Severson-Group/AMDS/Mainboard/REV20200407C/README.md

This folder contains schematics pdf, PCB pdf, bill of material (BOM), 3-D PCB, gerber files and all the required files to fabricate the boards.

## How to order 10 PCB boards

1. Place a new quote in https://www.pcbway.com/ 

2. Use the following table to set the pcb properties.

| Question | Answer |
|---|---|
|Size| 203.4 x 203.4 mm|
|Layer| 4 Layers|
|Quantity| 10|
|Board type| Single pieces|
|Different Design in Panel| 1|
|Material: FR-4| TG150|
|Thickness| 1.6 mm|
|Min Track/Spacing| 6/6mil|
|Min Hole Size| 0.3mm|
|Solder Mask| Black|
|Silkscreen| White|
|Gold fingers| No|
|Surface Finish| HASL with lead|
|"HASL" to "ENIG"| No|
|Via Process| Tenting vias|
|Finished Copper| 1 oz Cu (Inner Copper: 1 oz)|
|Additional options| UL Marking: None|

3. Upload the gerbers from `SensorMotherBoard_REVC_Gerber\` folder.

4. Place the order, it should arrive in 7-9 days.

## How to order components for the board

1. The components sheet can be found in `SensorMotherBoard_REVC_BOM\` folder.

2. Upload the BOM sheet in https://www.digikey.com/ordering/shoppingcart.

3. Place the order.
