Severson-Group/AMDS/CurrentCard/REV20190618A/README.md

# SensorCard
Voltage and Current Sense Board
