Severson-Group/AMDS/Accessories/DaisyChainAdapter/REV20260129A/README.md

# Daisy Chain Adapter REV20260129A

This folder contains the compiled design outputs for the Daisy Chain Adapter. This includes the schematics, images of the PCB layout, the bill of materials (BOM), and the files needed to order fully populated boards from an online vendor.

## Board Parameters

| Question | Answer |
|---|--- |
| Board Size | 2.17" x 2.80" |
| Number of Layers | 4 Layers |
| Double Sided | Yes |
| Surface Finish | Tin lead |
| Silkscreen | White |
| Material | FR-4, TG150 |
| Board Thickness | 1.6 mm |
| Min Trace Spacing | 0.127 mm (5 mil) |
| Min Hole Size | 0.36 mm (14 mil) |
| Number of Holes | 78 |
| Solder Mask | Green |
| HASL or ENIG | No |
| Finished Copper | 1 oz |

## Assembly Details

| Question | Answer |
|---|---|
| Unique Part Count[^1] | 14 |
| Number of Total Parts[^1] | 29 |
| Total SMT Part Count | 26 |
| Total Through-hole Part Count | 3 |
| Total Mechanical Screws | 4 |
| Total Mechanical Standoffs | 4 |
| BGA / QFN | No |

## Bill of Materials

The [Bill of Materials (BOM)](daisy-chain-bom.csv) contains components for 1 board. If users of this repo discover that any components are unavailable, please maintain an `alternate-components.md` file in this folder that lists approved alternates.

[^1]: This number does not include screws or standoffs. With screws and standoffs included, the unique part count is 16 and total parts is 37. Users are advised to not have their assembly vendor place screws and standoffs.
