Severson-Group/AMDS/CurrentCard/REV20190618A/CurrentSensorBoard.pdf

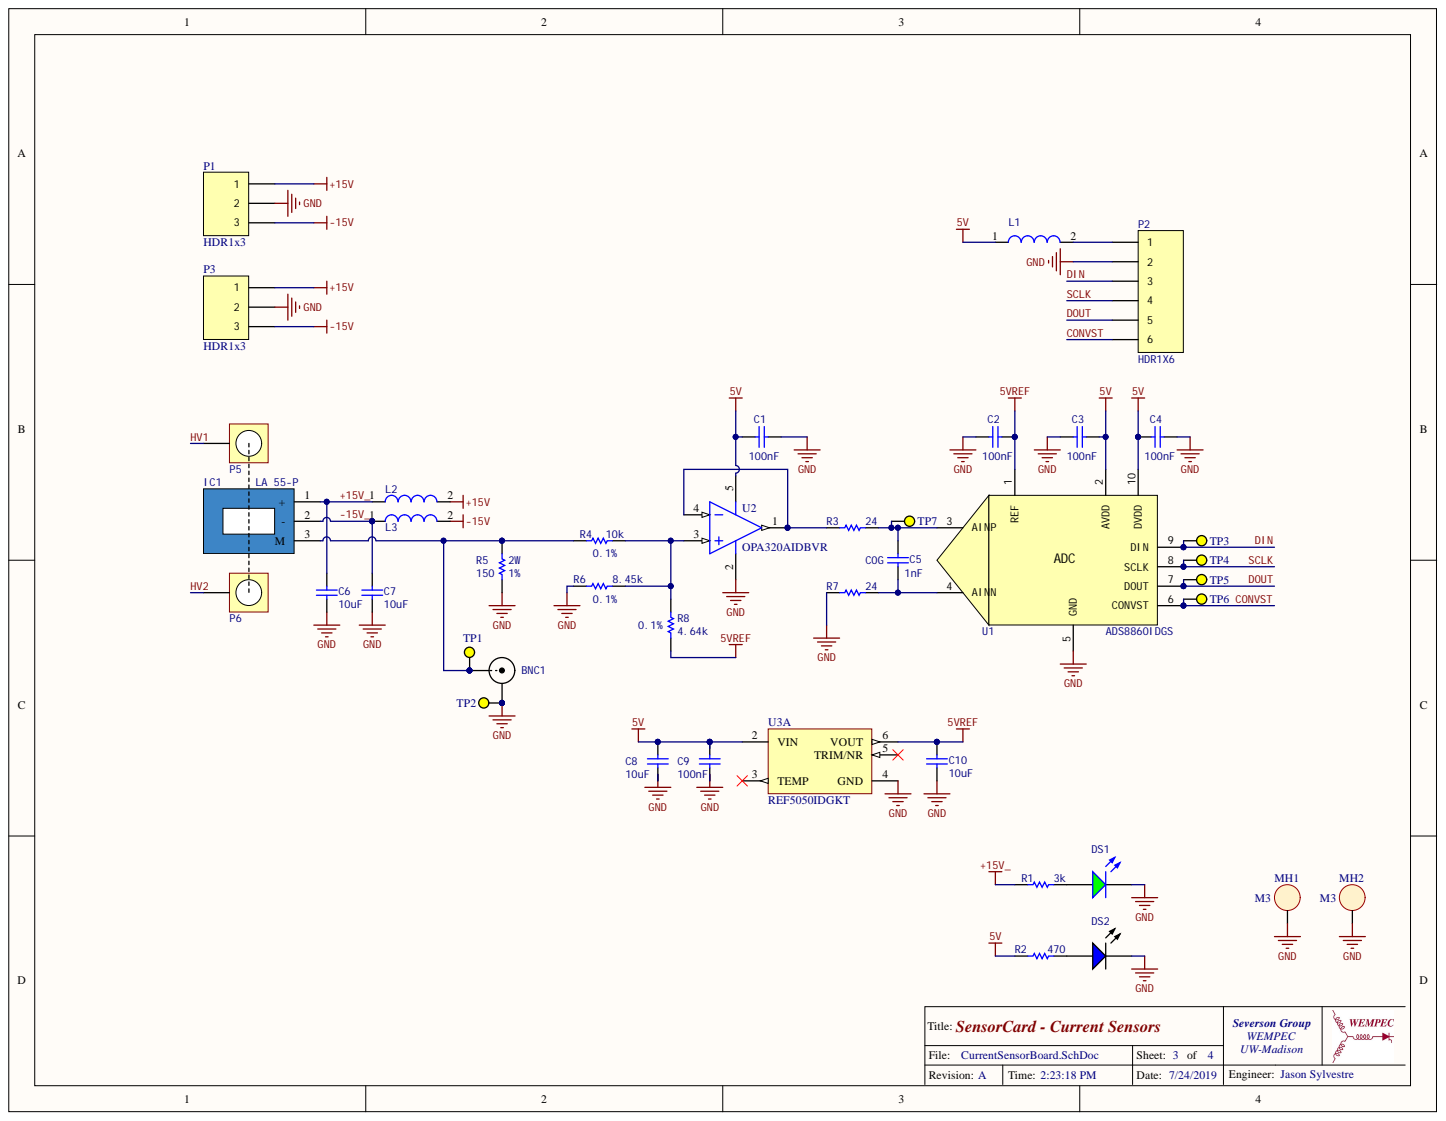
[picture p28: page 1]

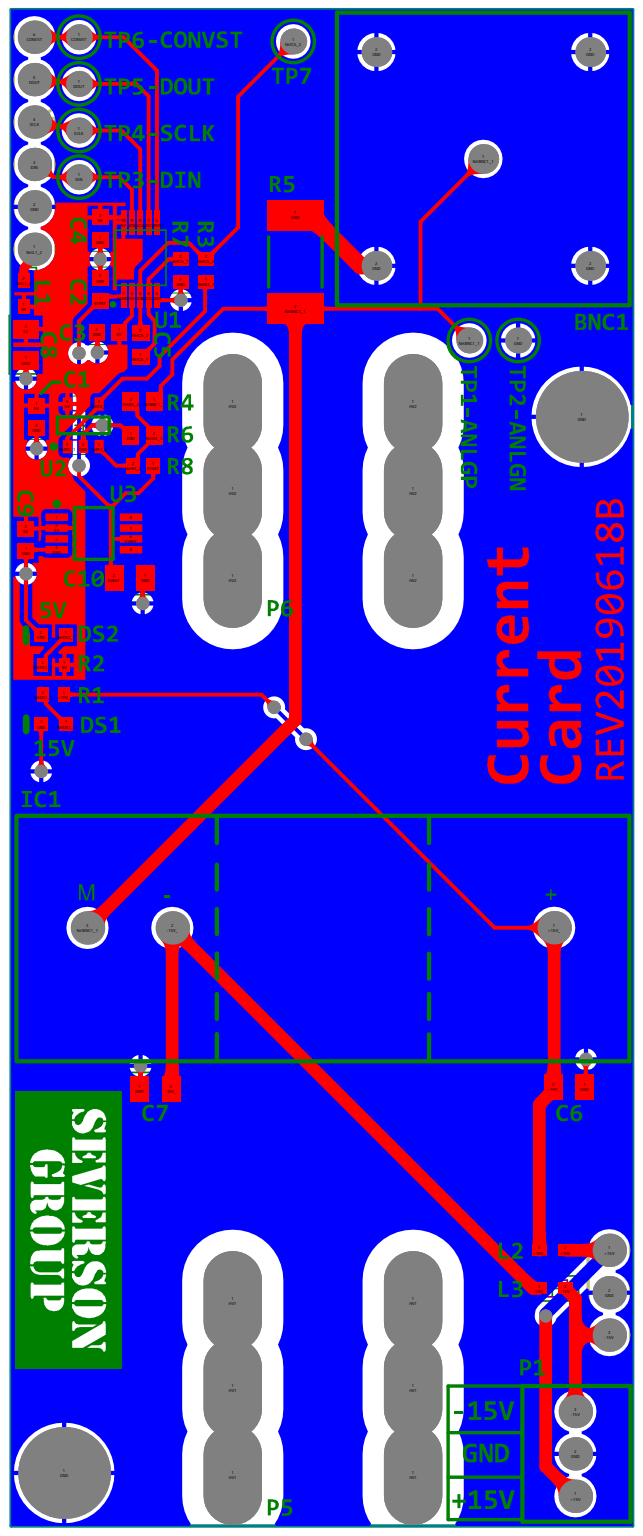
[picture p29: page 2]

2 NetC5_1 | 2 NetC5_2

GND

GND 1 GND | 5VREF 5
