Severson-Group/AMDS/CurrentCard/REV20190805B/CurrentSensorBoard.pdf

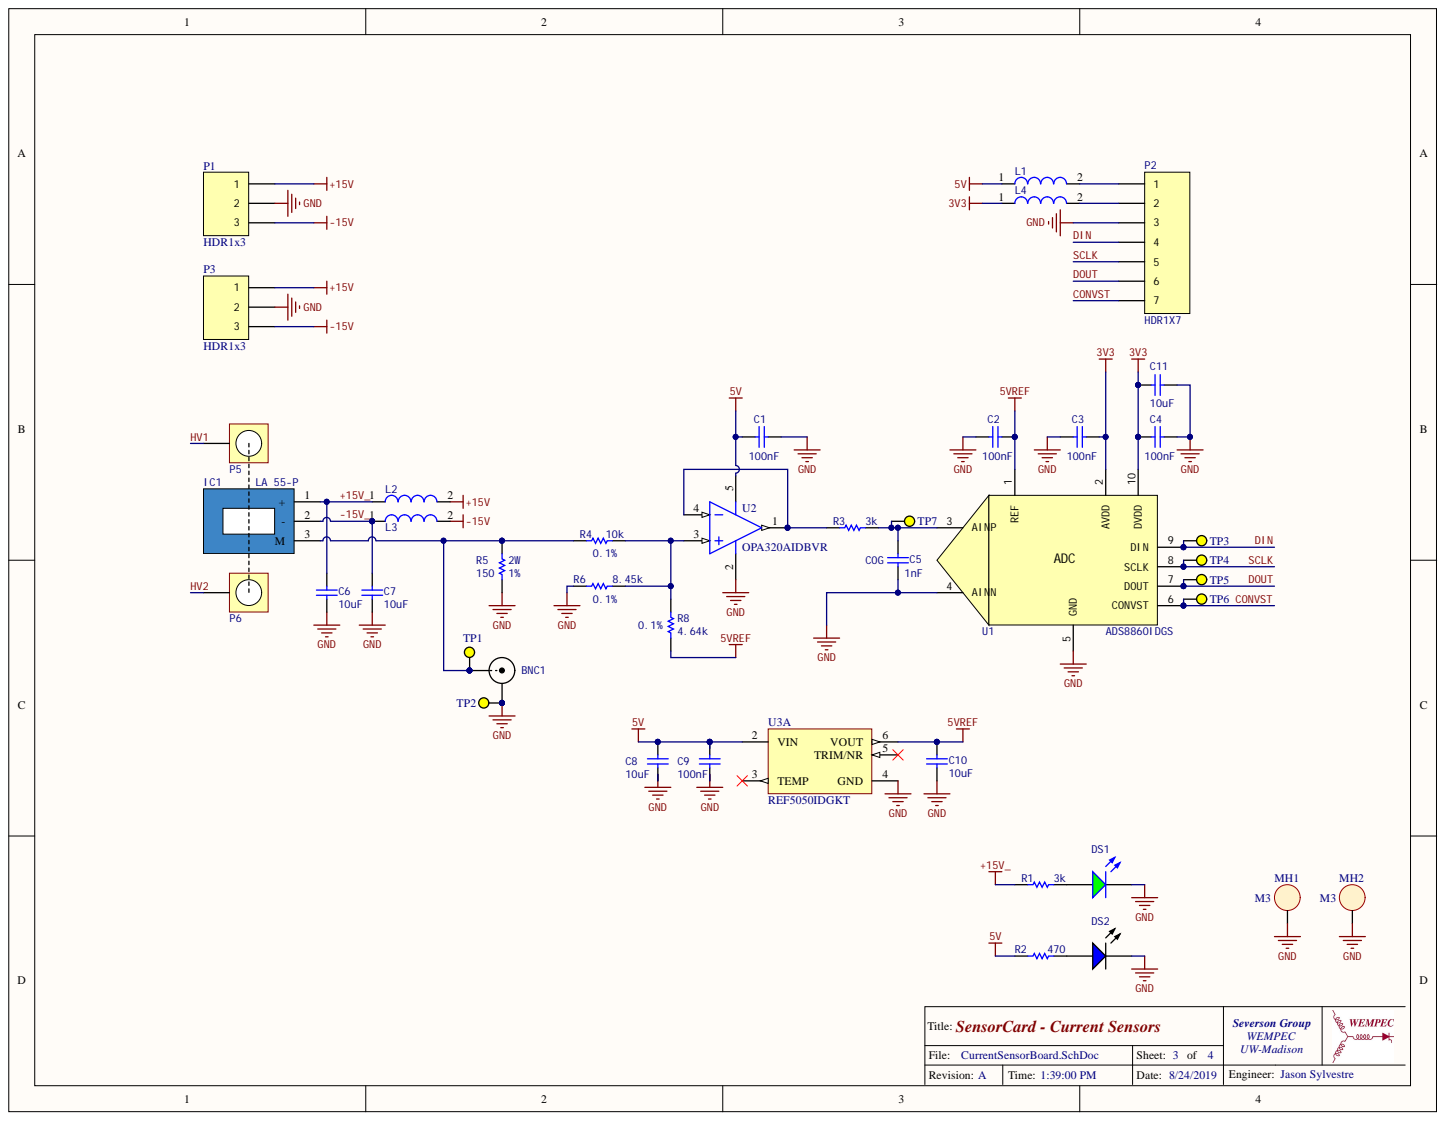
[picture p30: page 1]

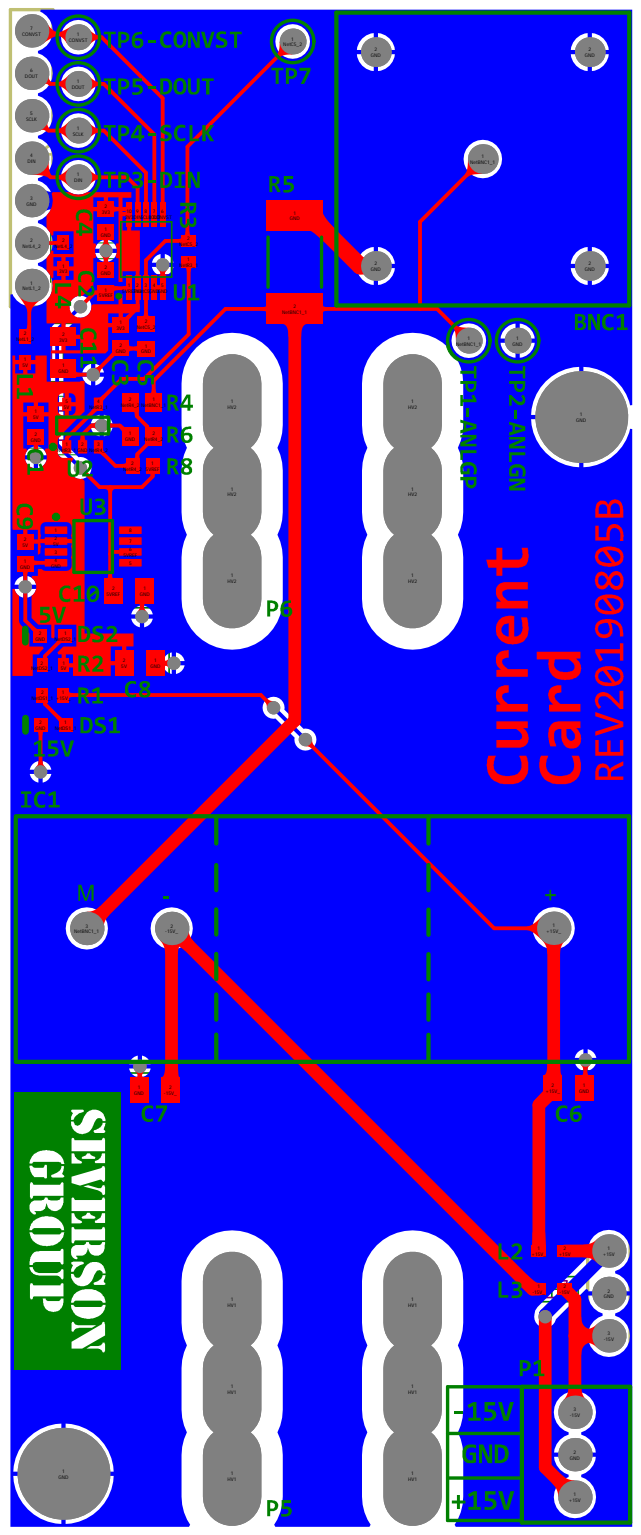
[picture p31: page 2]

1 GND GND | 5VREF 5
