Severson-Group/AMDS/HighVoltageCard/REV20190618A/VoltageSensorBoard.pdf

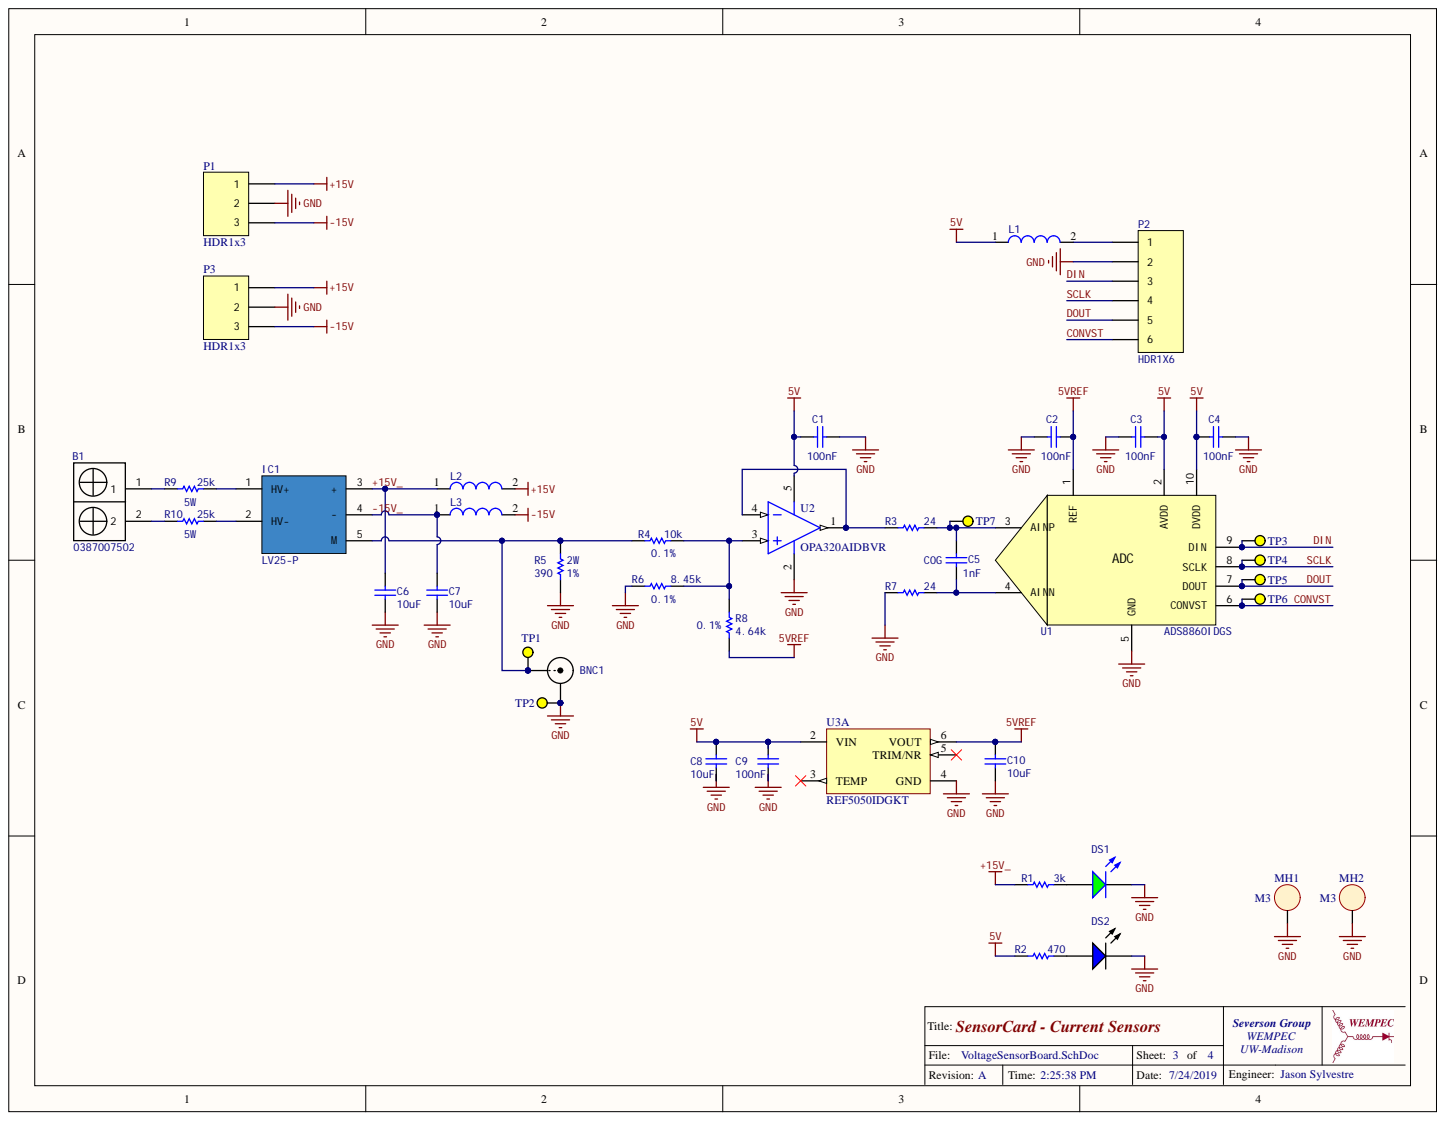
[picture p32: page 1]

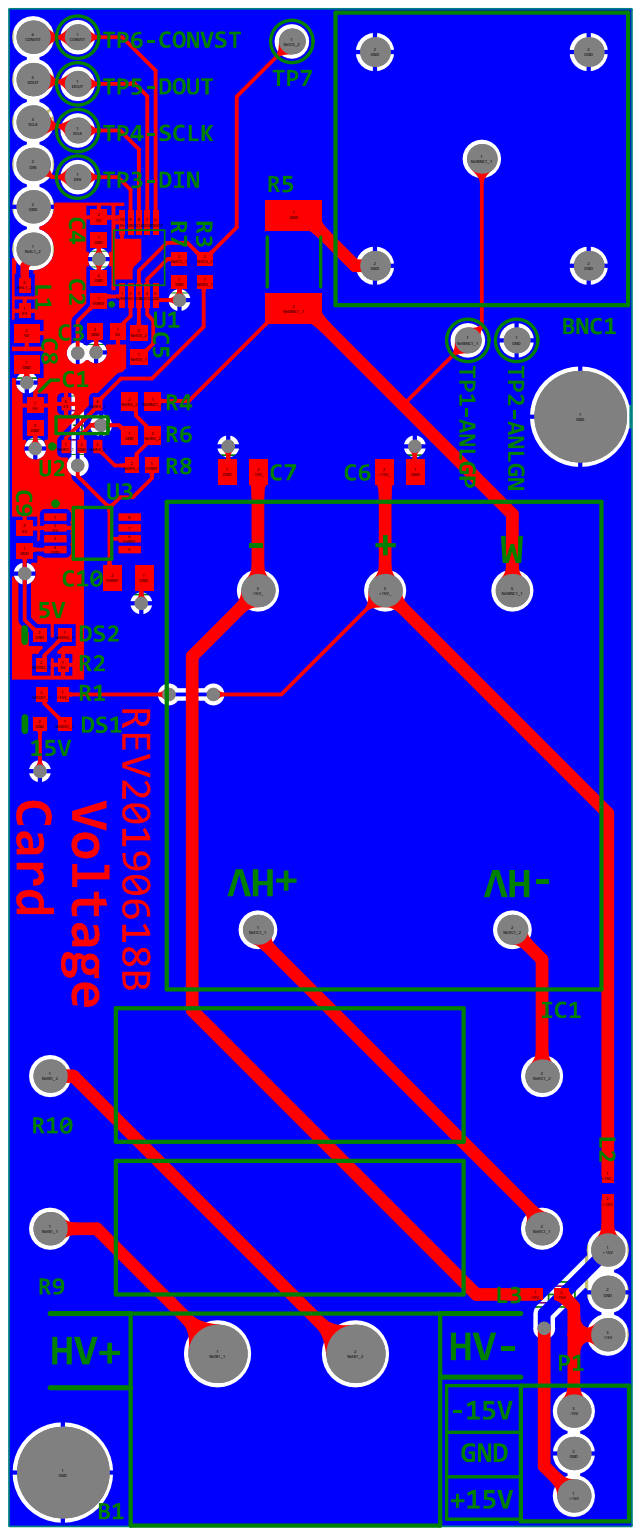
[picture p33: page 2]

2 NetC5_1 | 2 NetC5_2

1 5V | 5 5V | NetR3_1 | 2 | 1 NetBNC1_1

NetDS1_1 2 +15V_ 1 | NetIC1_1 NetIC1_1 1 1
