Severson-Group/AMDS/HighVoltageCard/REV20190805B/VoltageSensorBoard.pdf

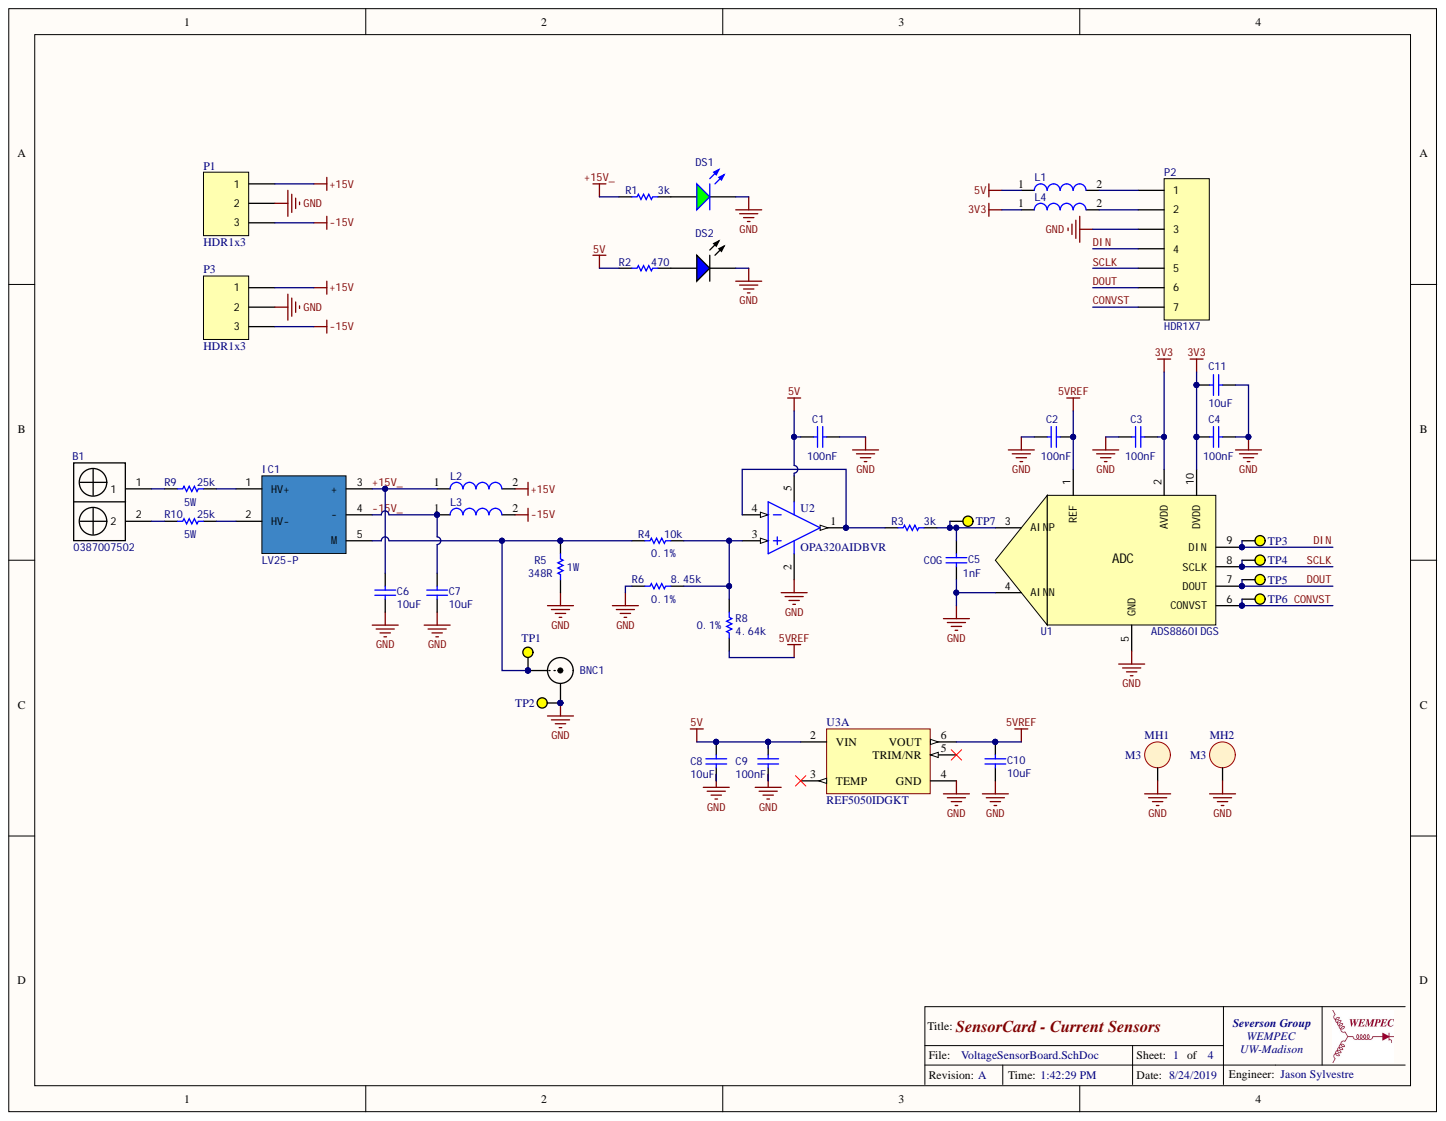
[picture p34: page 1]

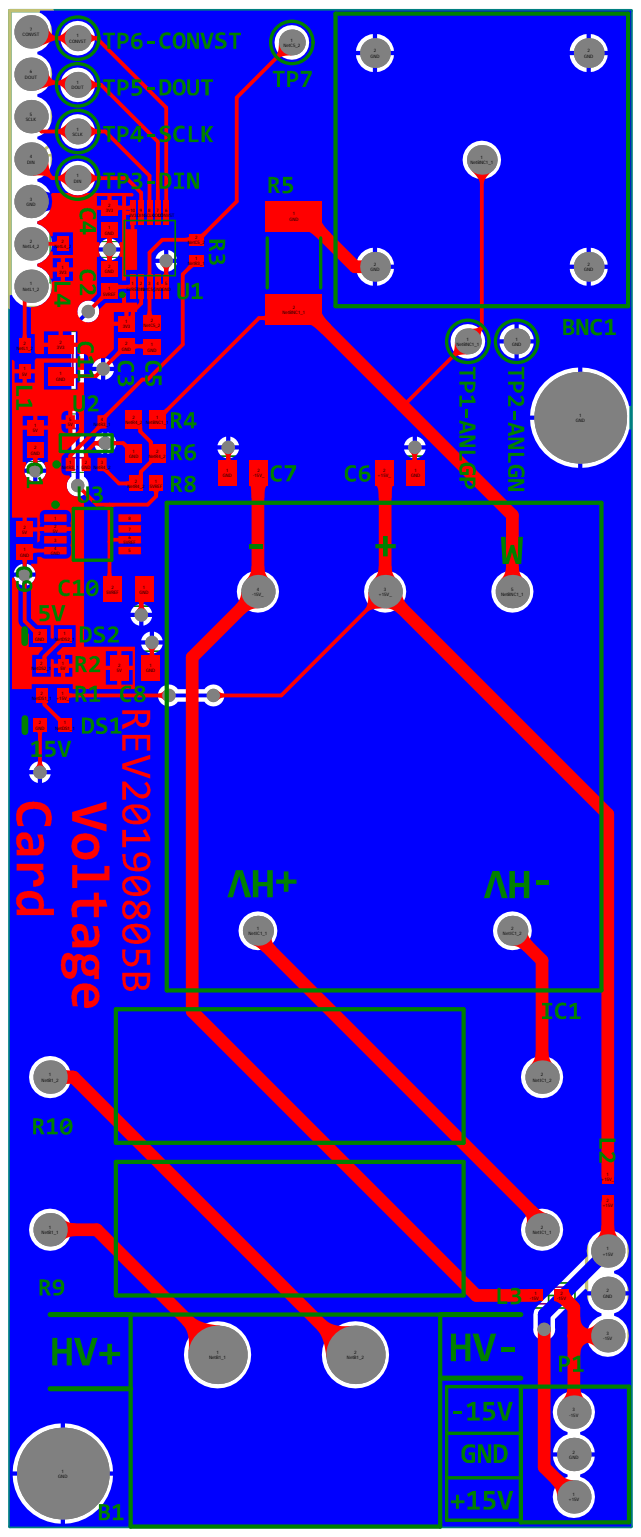
[picture p35: page 2]

5V | GND

NetDS1_1 2 +15V_ 1 | NetIC1_1 NetIC1_1 1 1
