Severson-Group/AMDS/Mainboard/REV20190805B/SensorMotherBoard.pdf

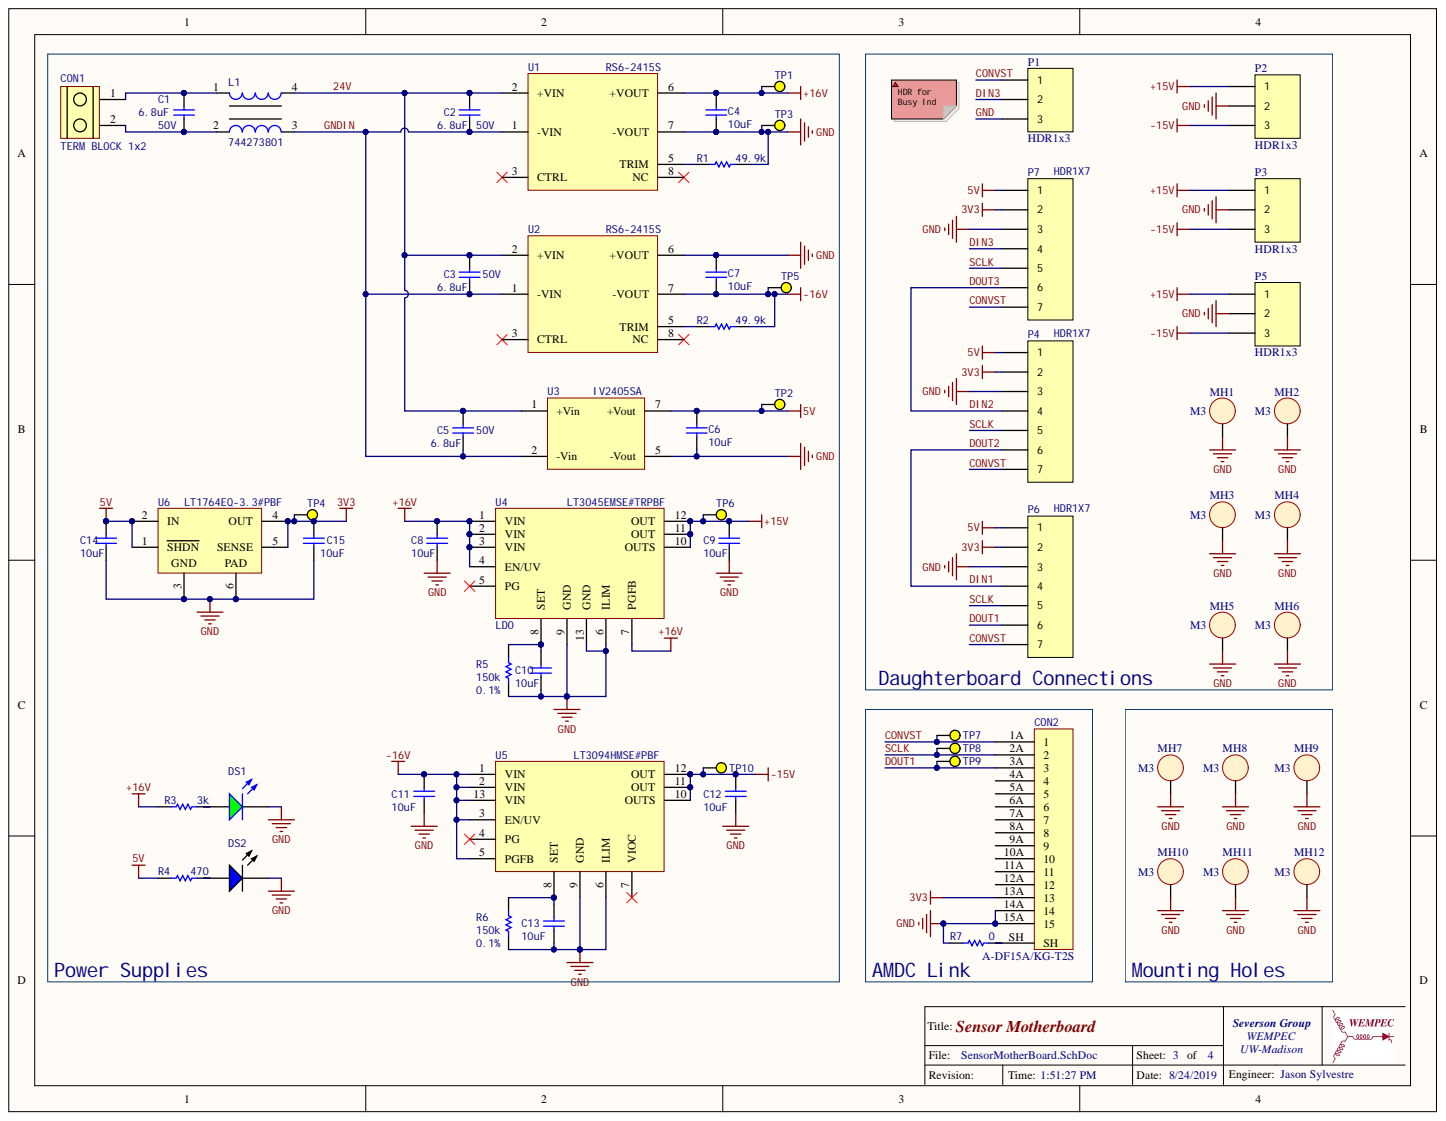
[picture p36: page 1]

C3 50V | -VIN 1 | C7 TP5

CONVST

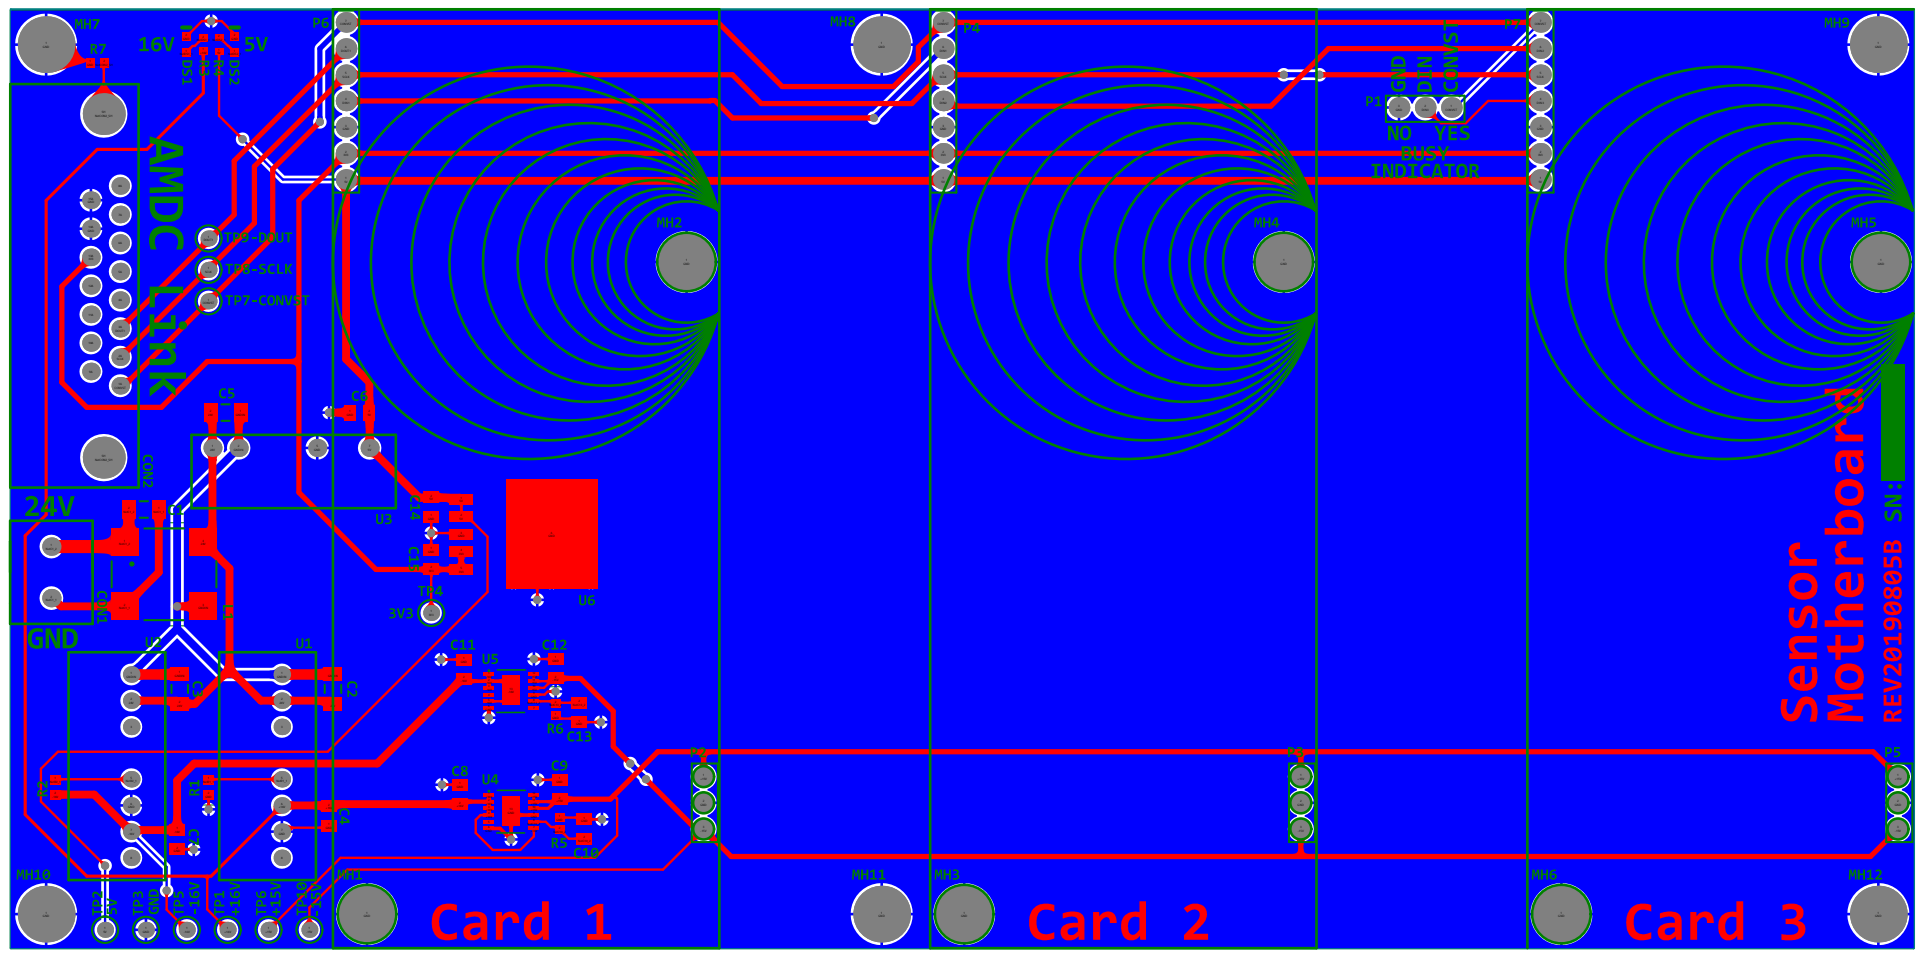
[picture p37: page 2]
