Severson-Group/AMDS/CurrentCard/REV20200830C/pcb-layers.pdf

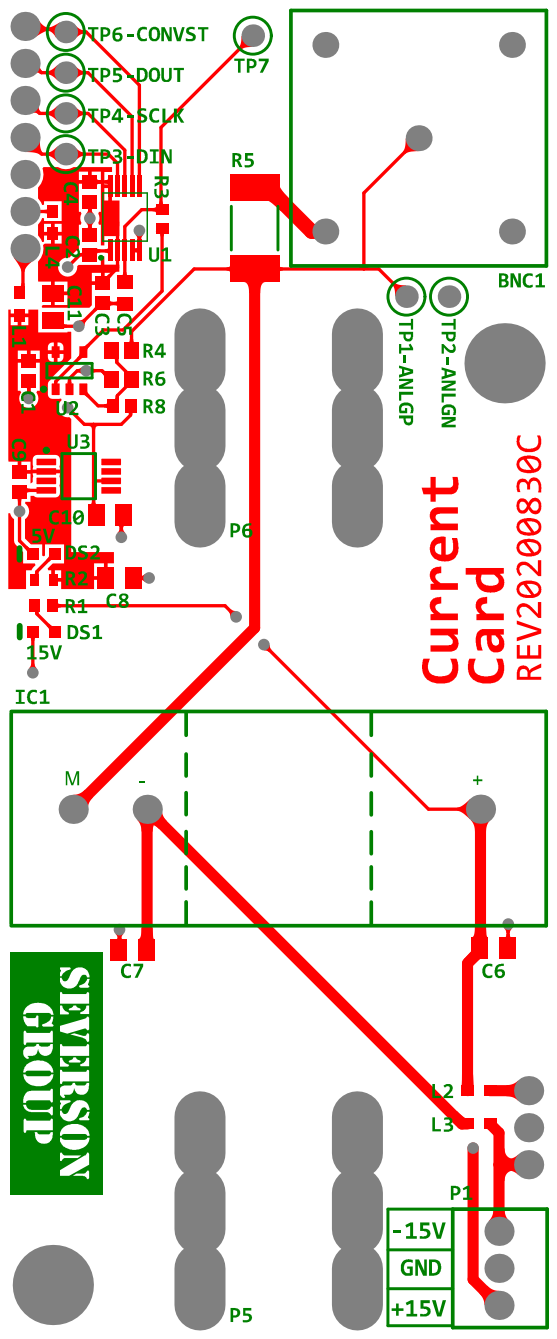
[picture p44: page 1]

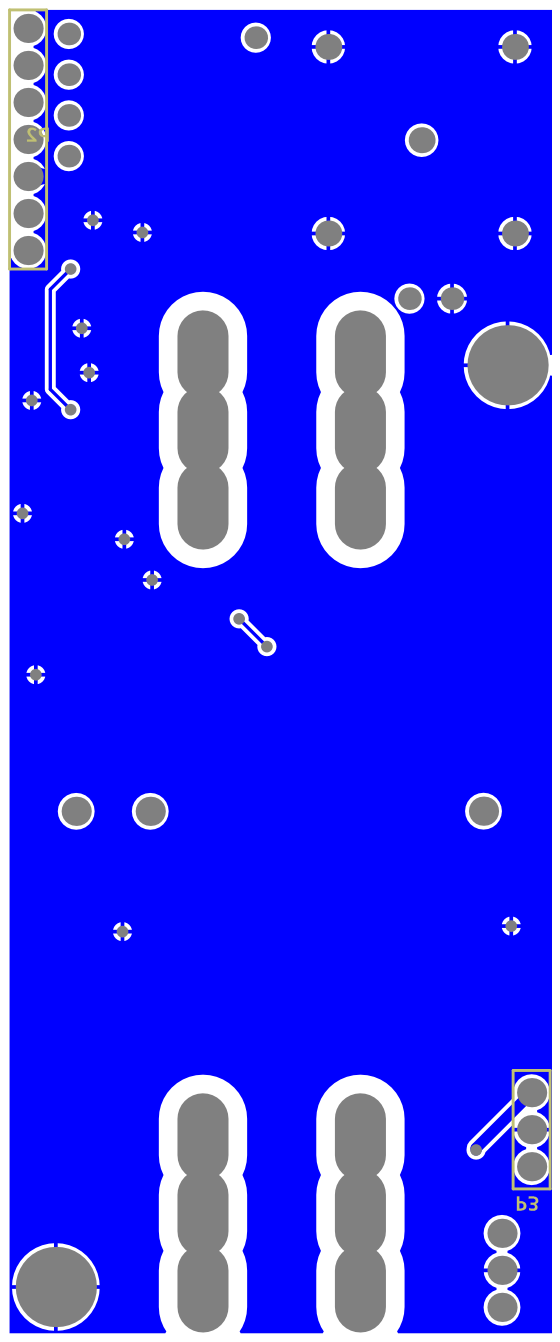
[picture p45: page 2]
