Severson-Group/AMDS/Mainboard/REV20200920D/pcb-layers.pdf

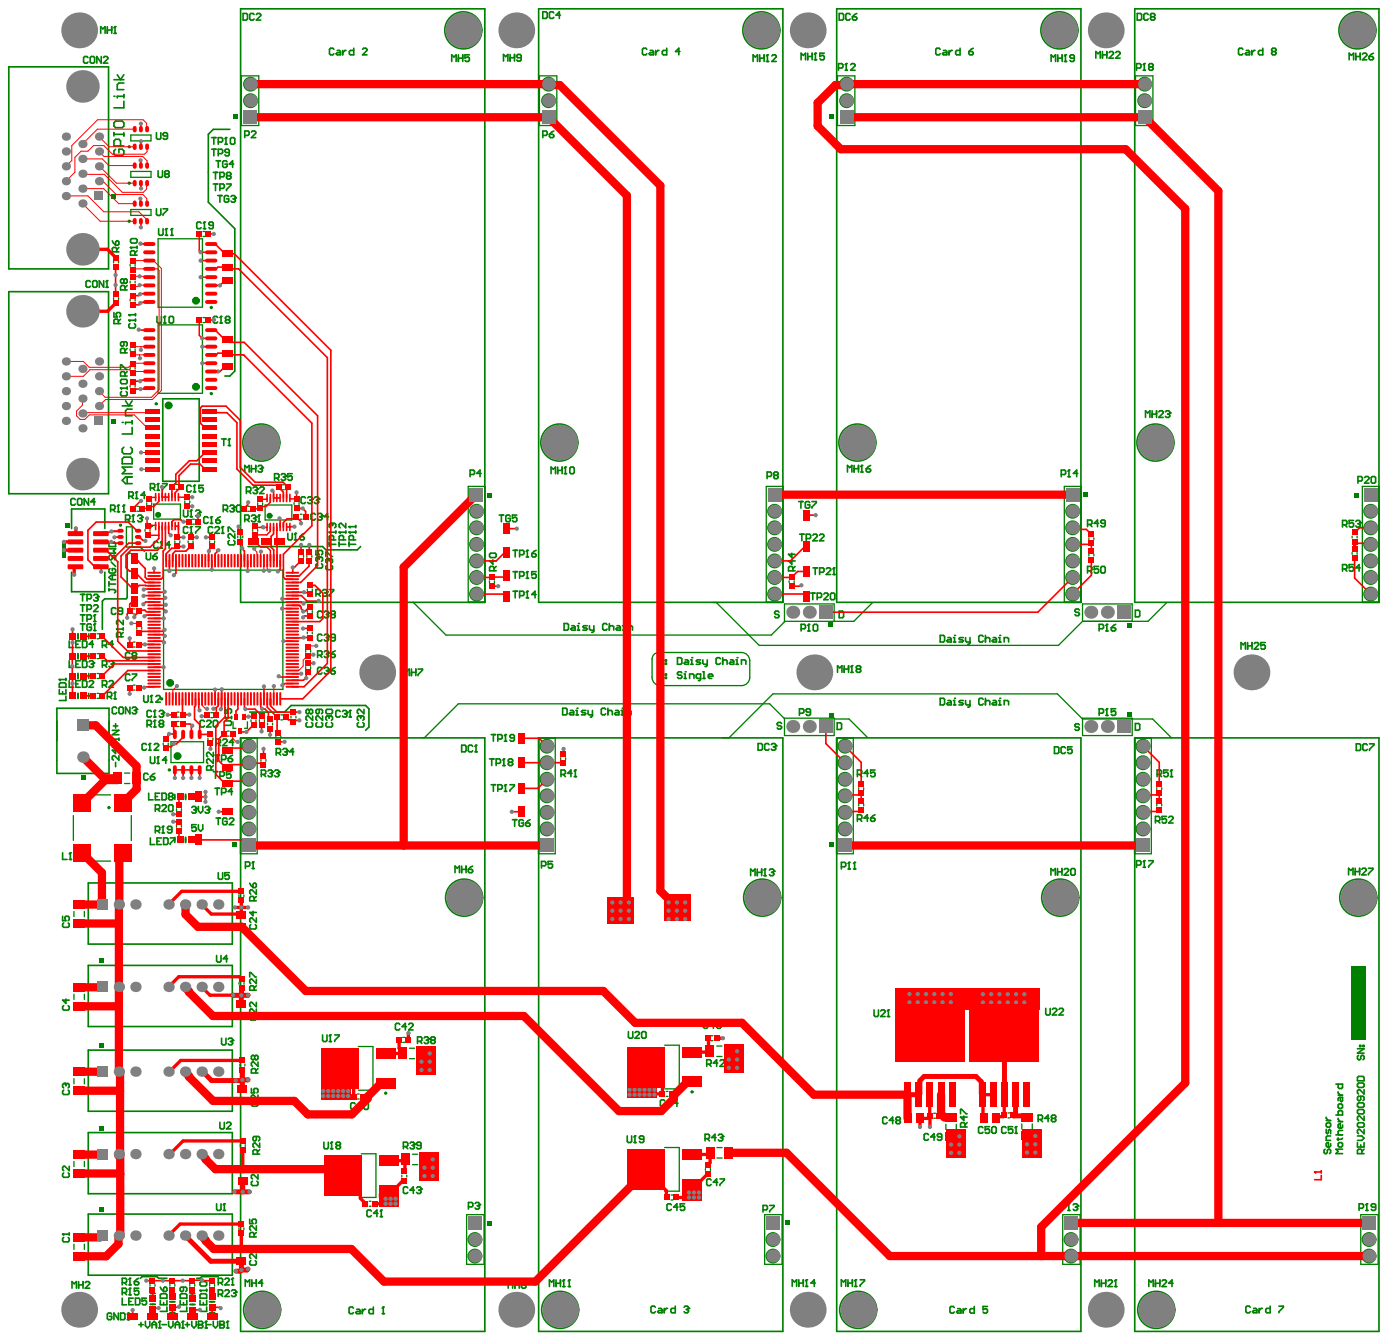
[picture p46: page 1]

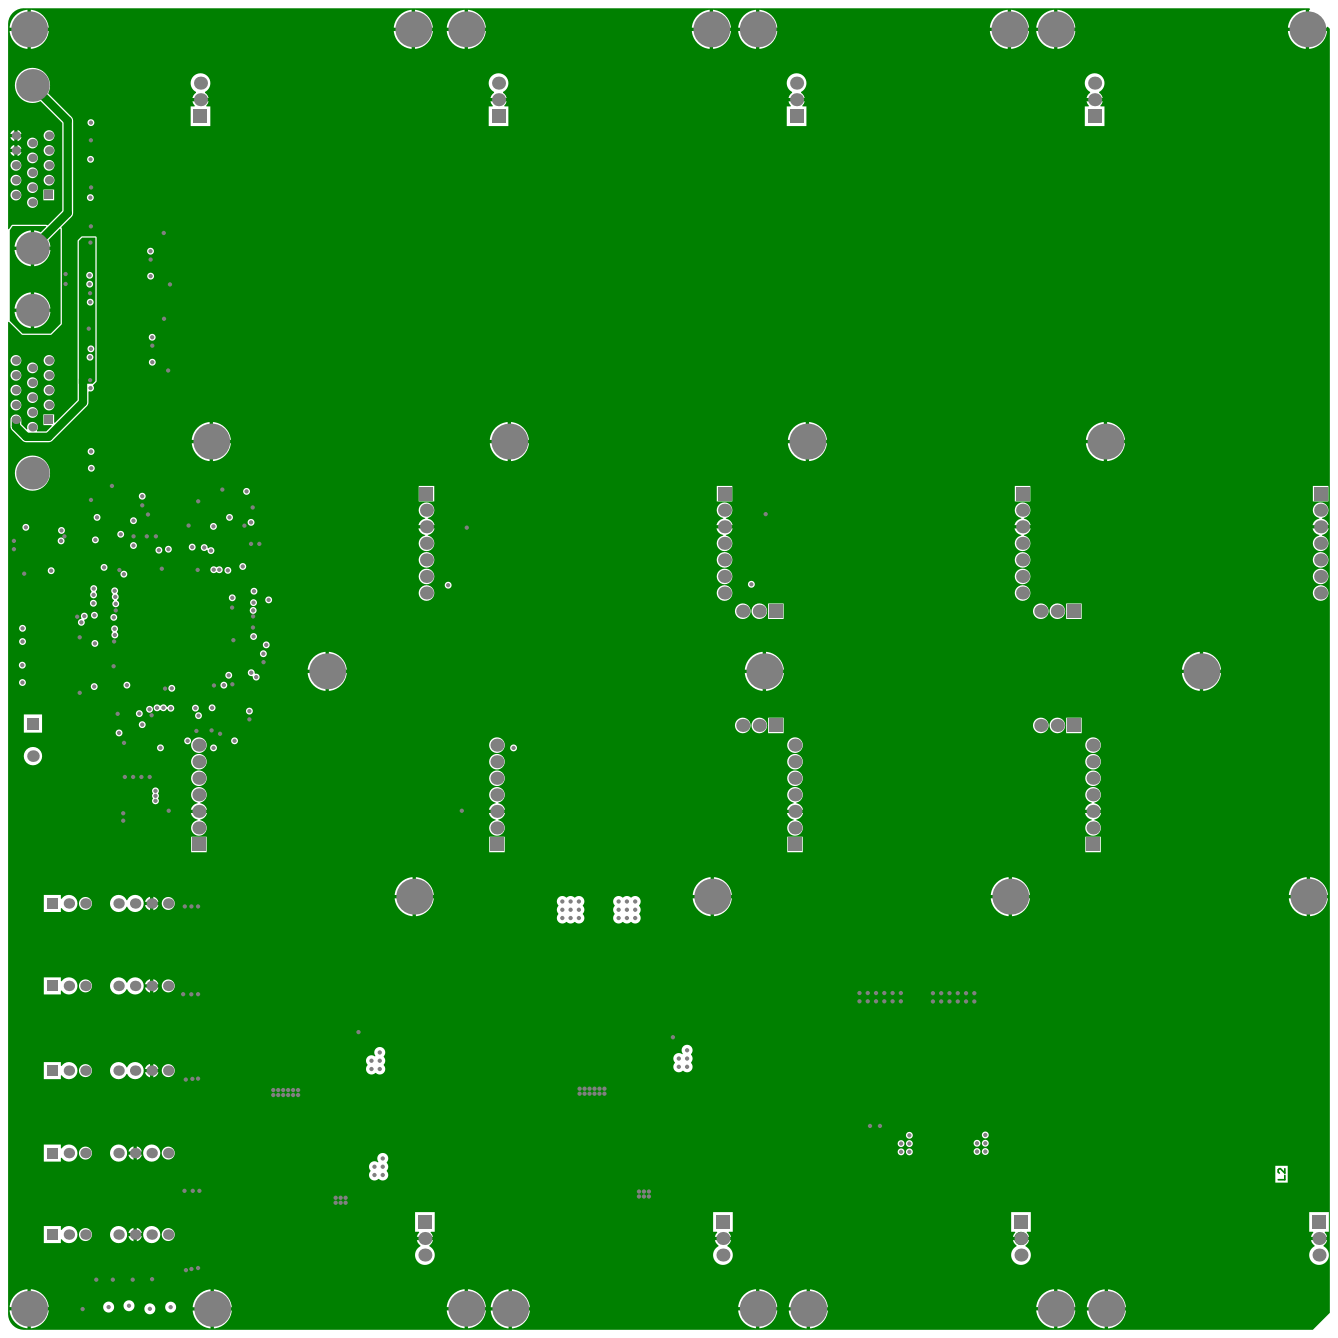
[picture p47: page 2]

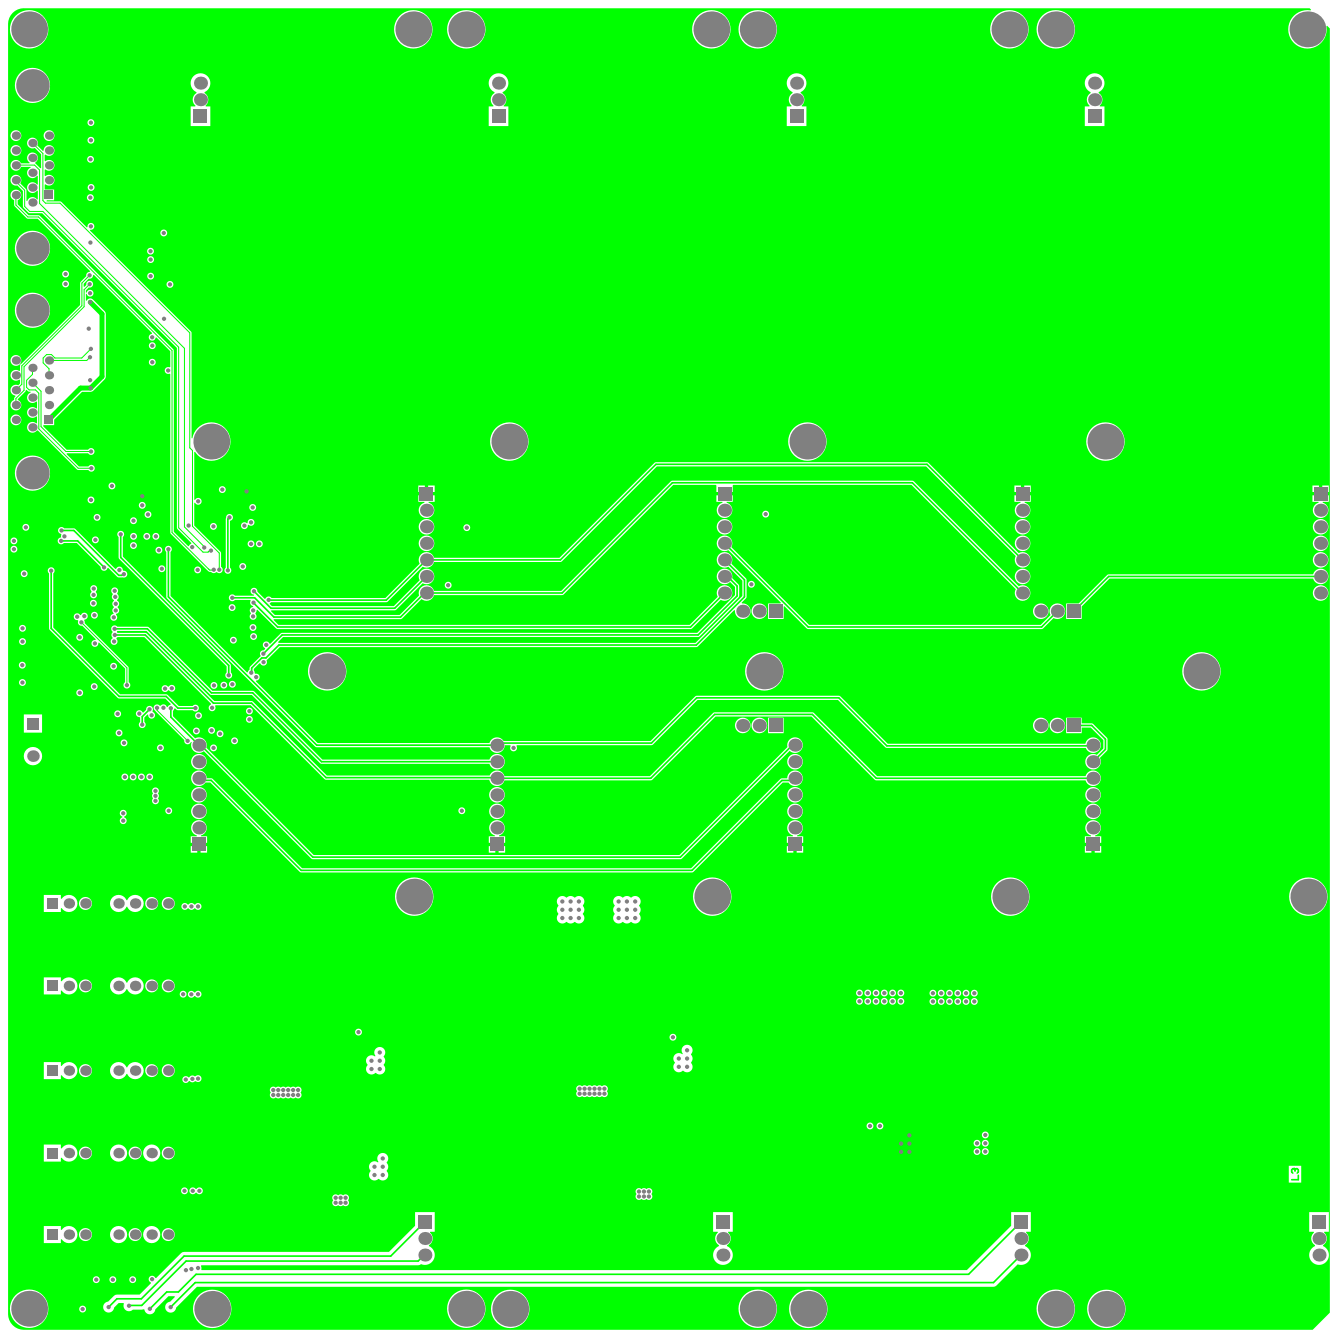
[picture p48: page 3]

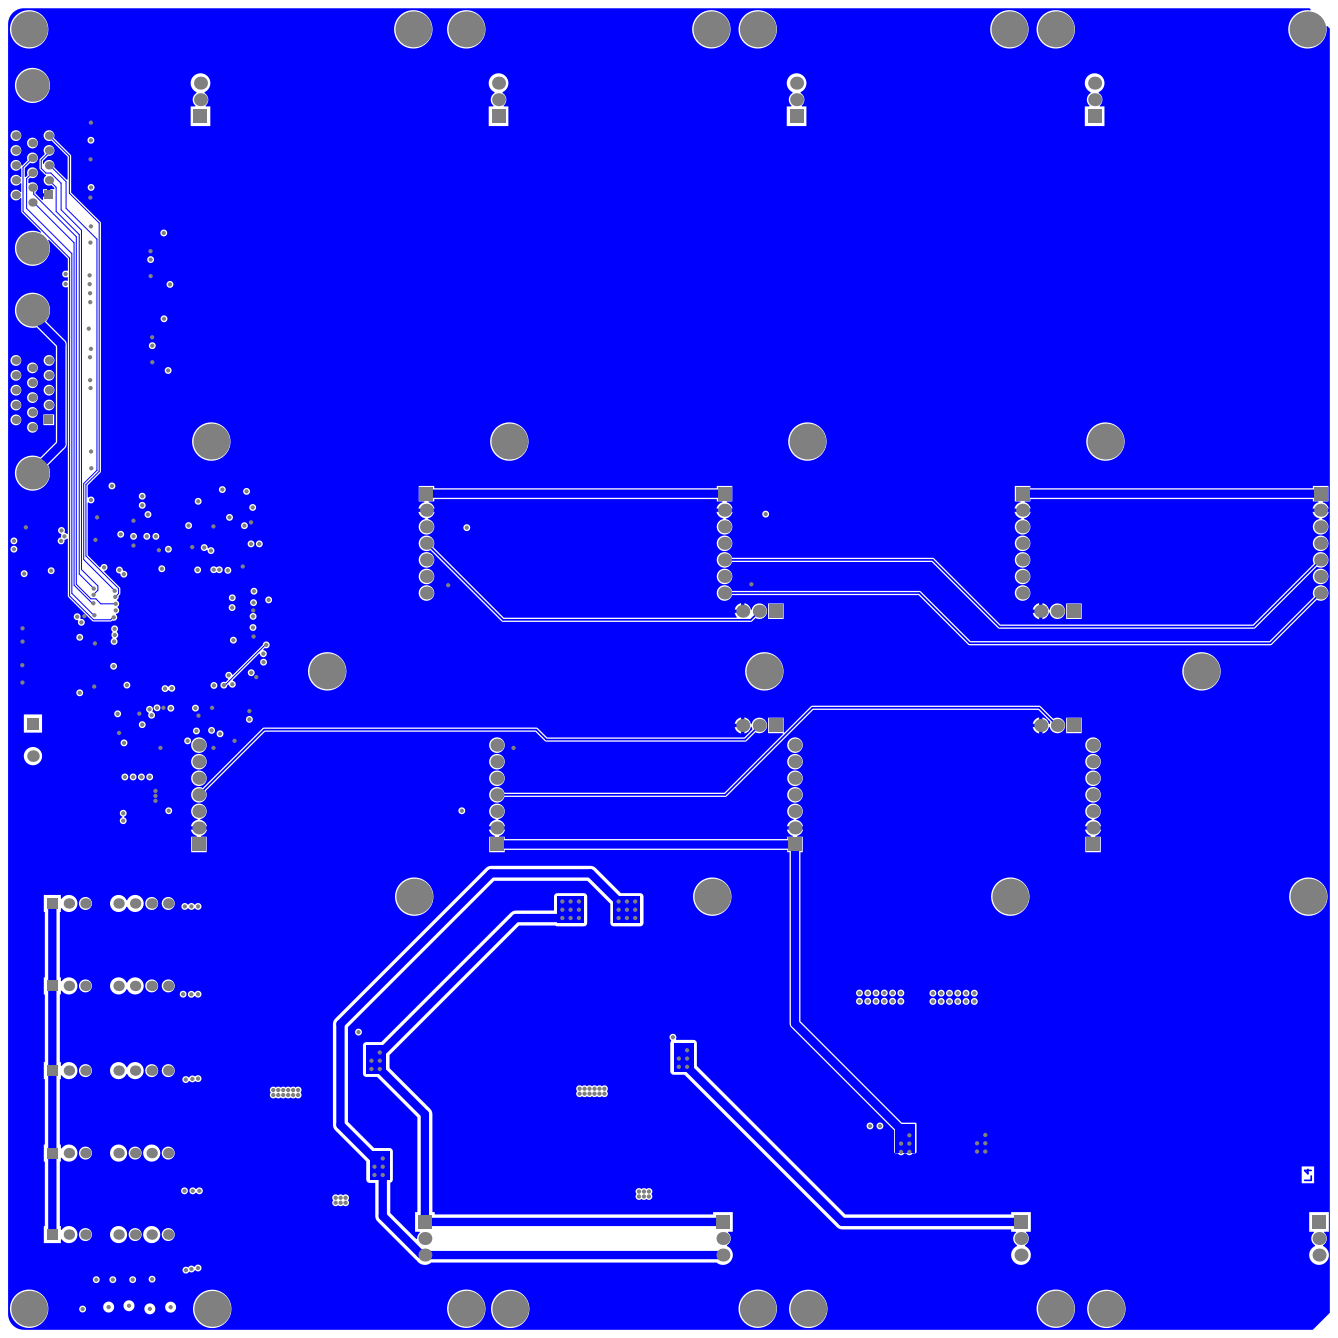
[picture p49: page 4]
