Severson-Group/AMDS/Mainboard/REV20190714A/SensorMotherBoard.pdf

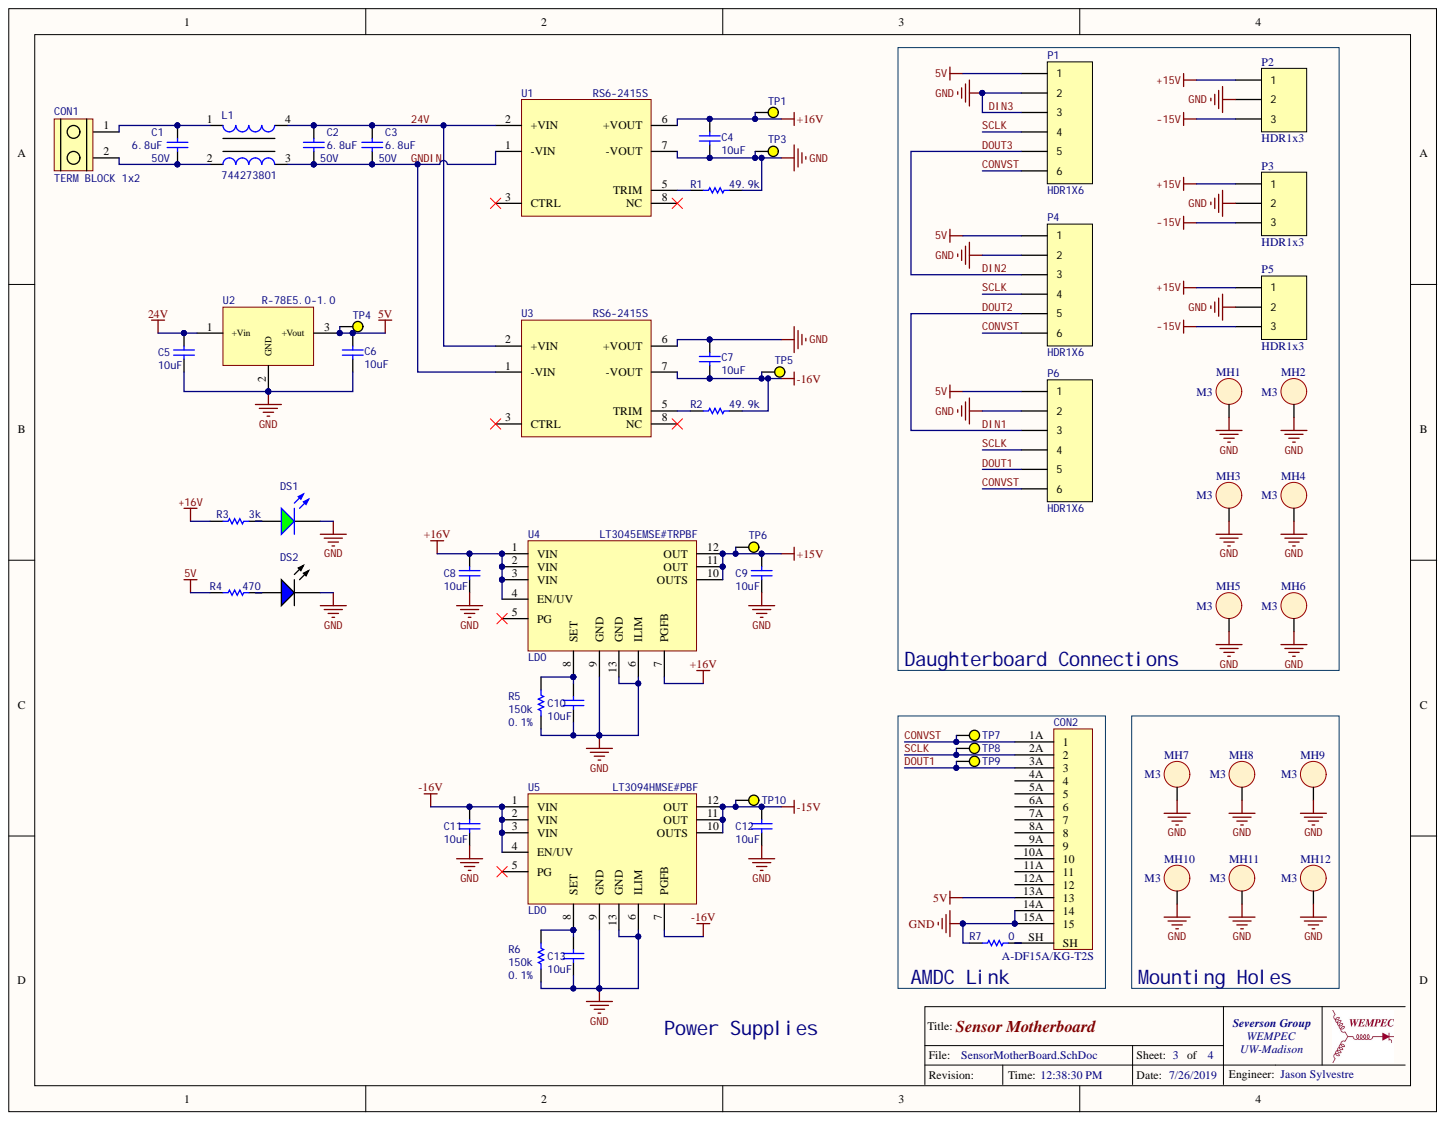
[picture p50: page 1]

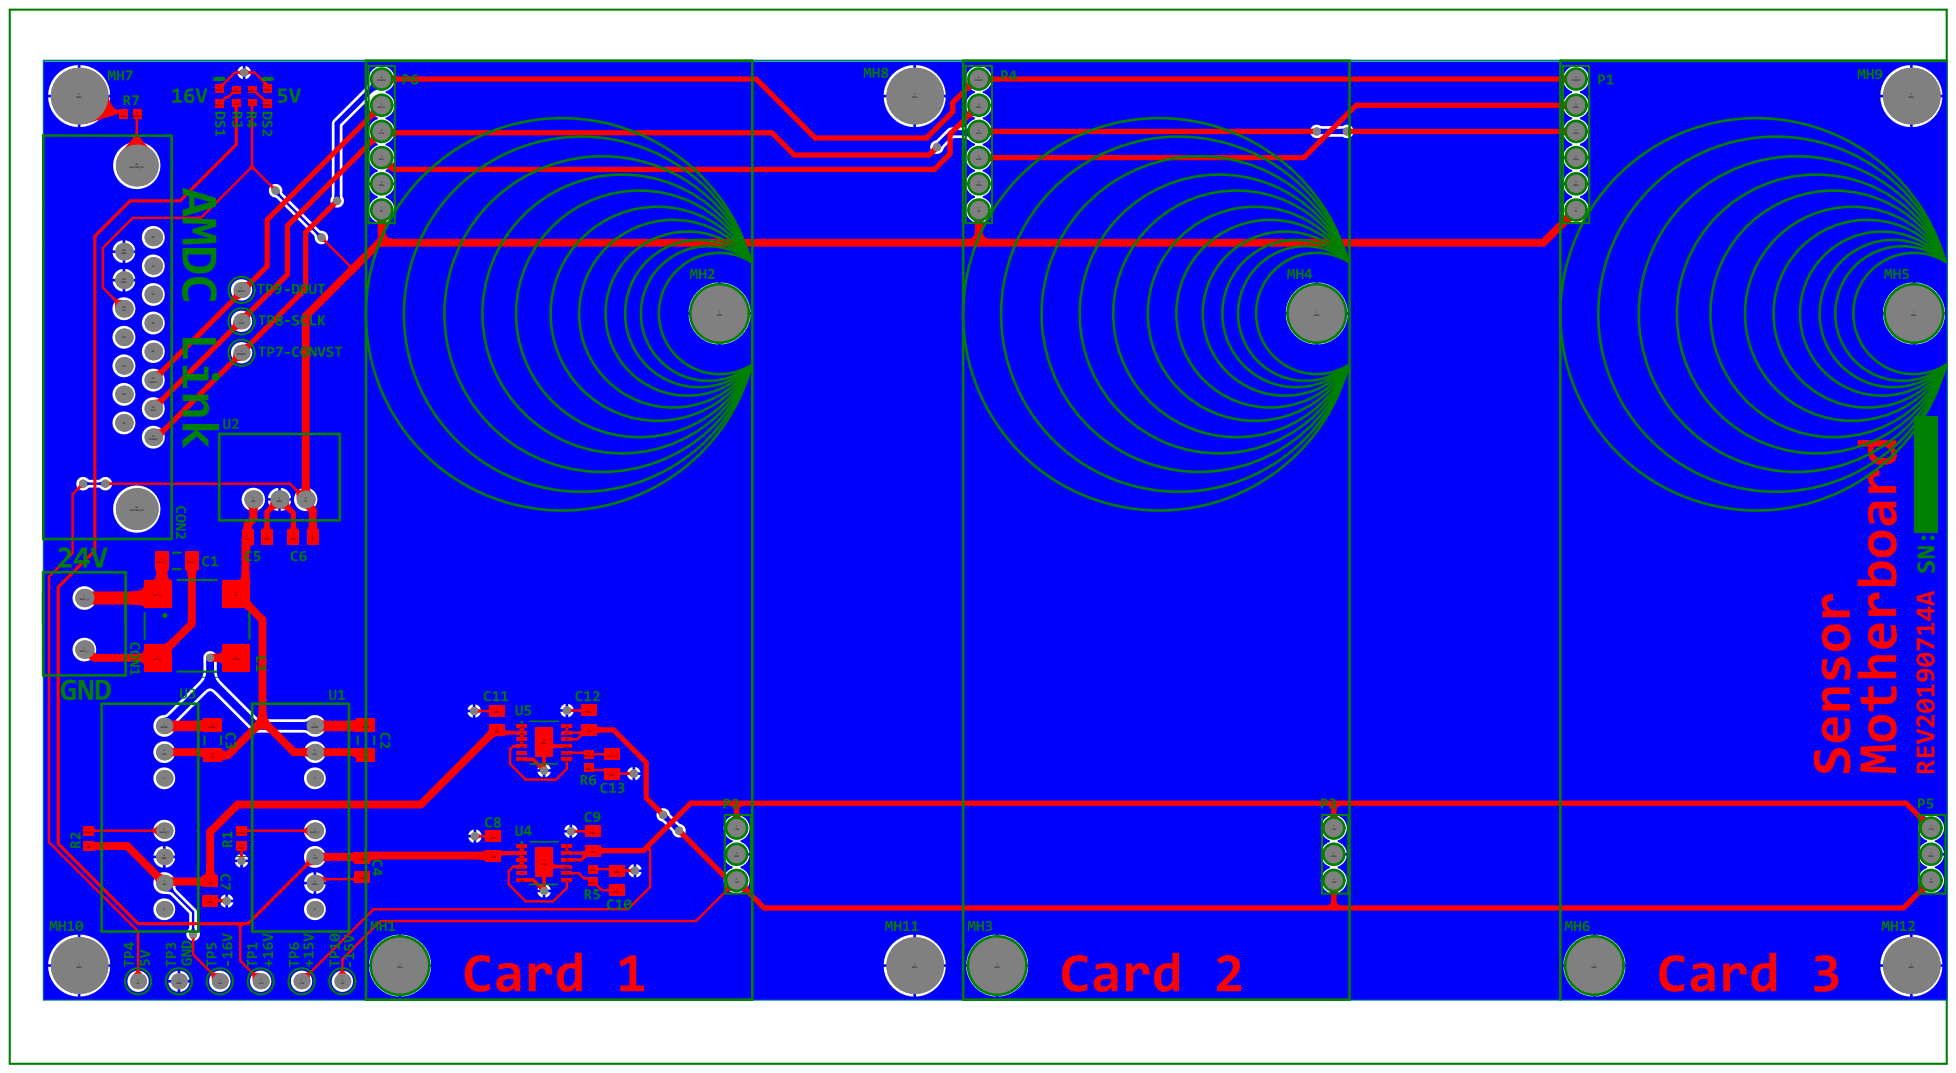
[picture p51: page 2]
