Severson-Group/AMDS/Accessories/DaisyChainAdapter/REV20260129A/pcb-layers.pdf

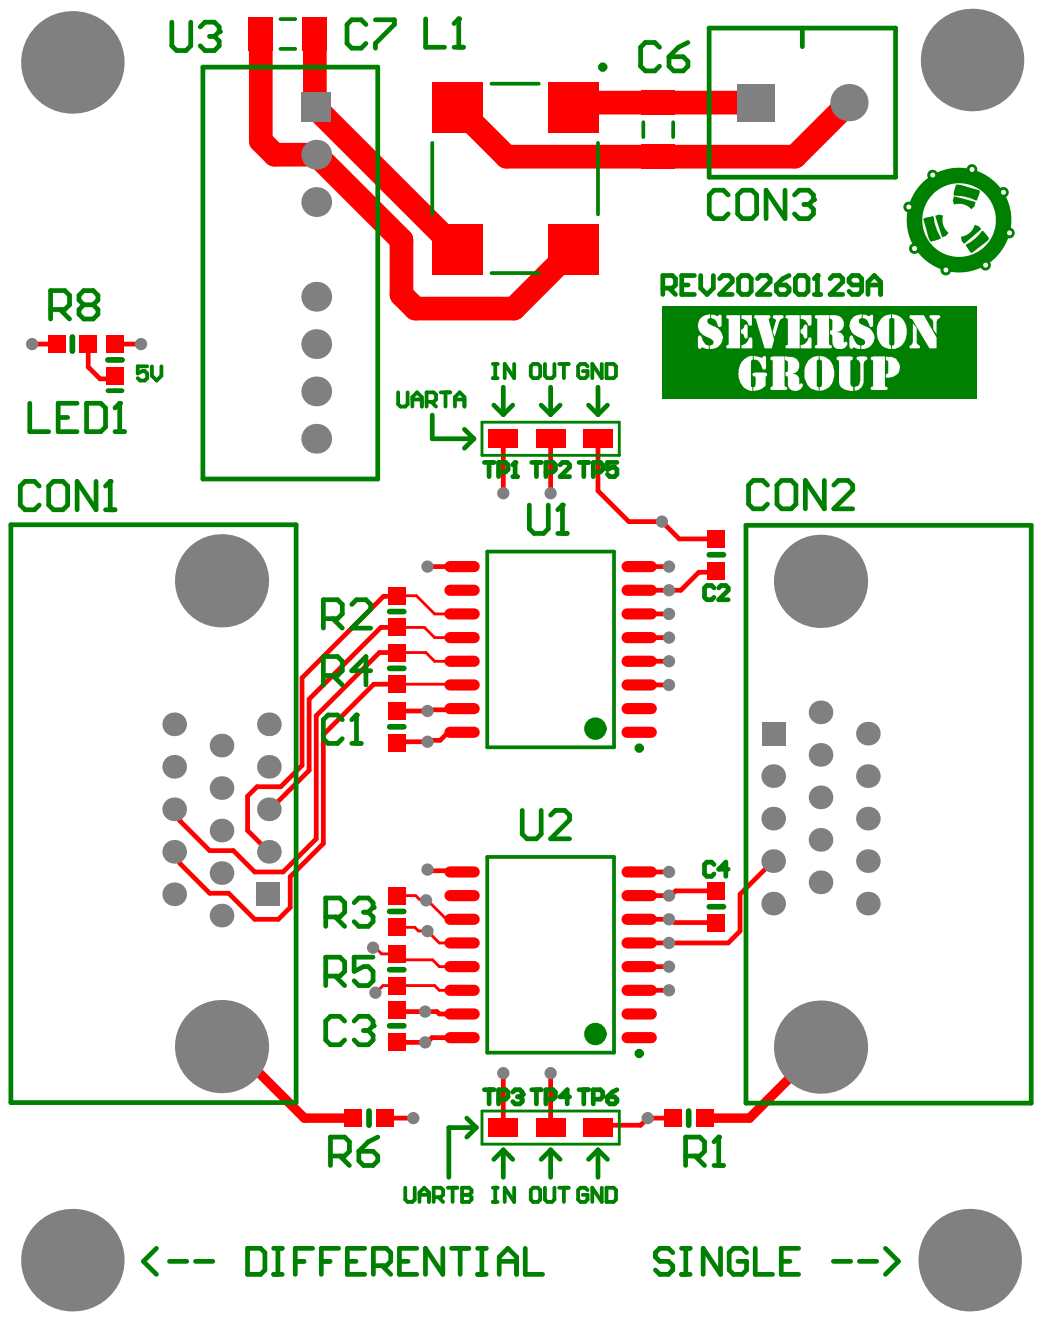
[picture p52: page 1]

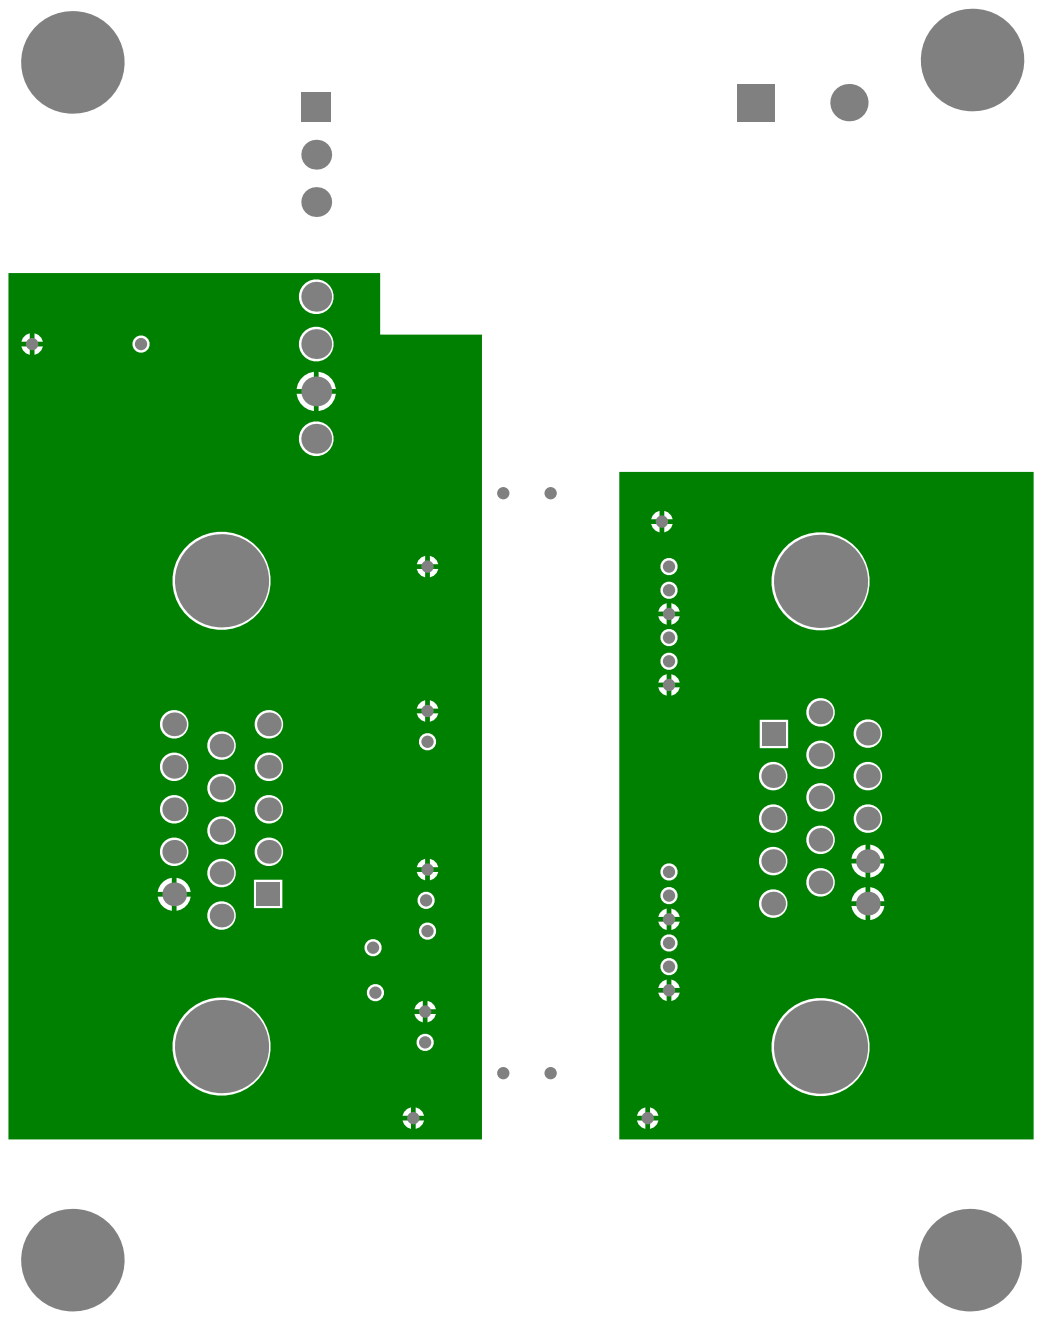
[picture p53: page 2]

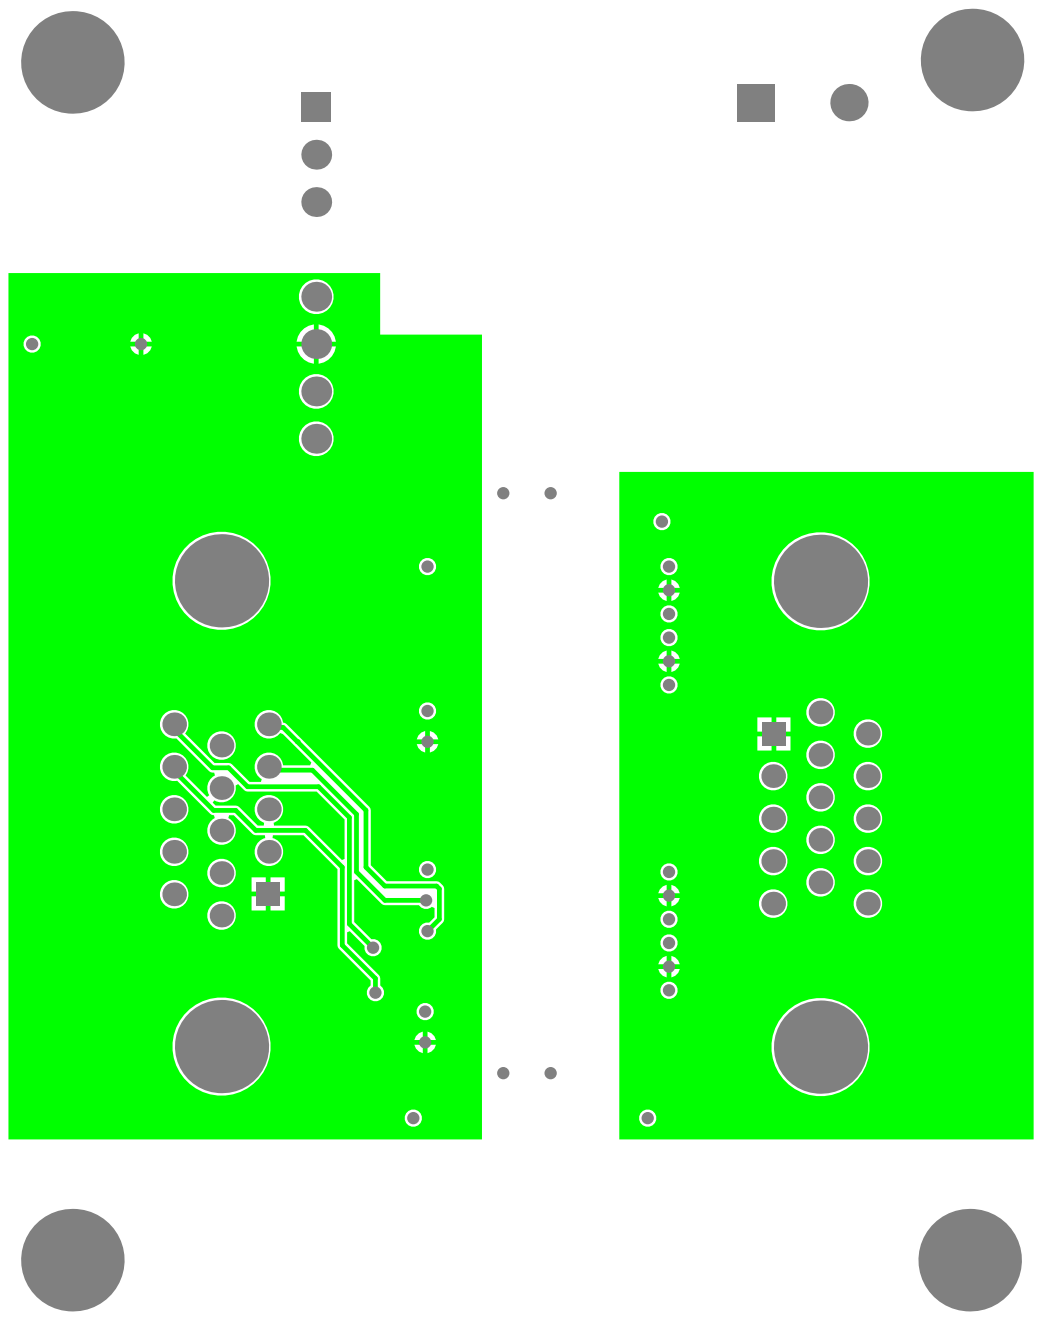
[picture p54: page 3]

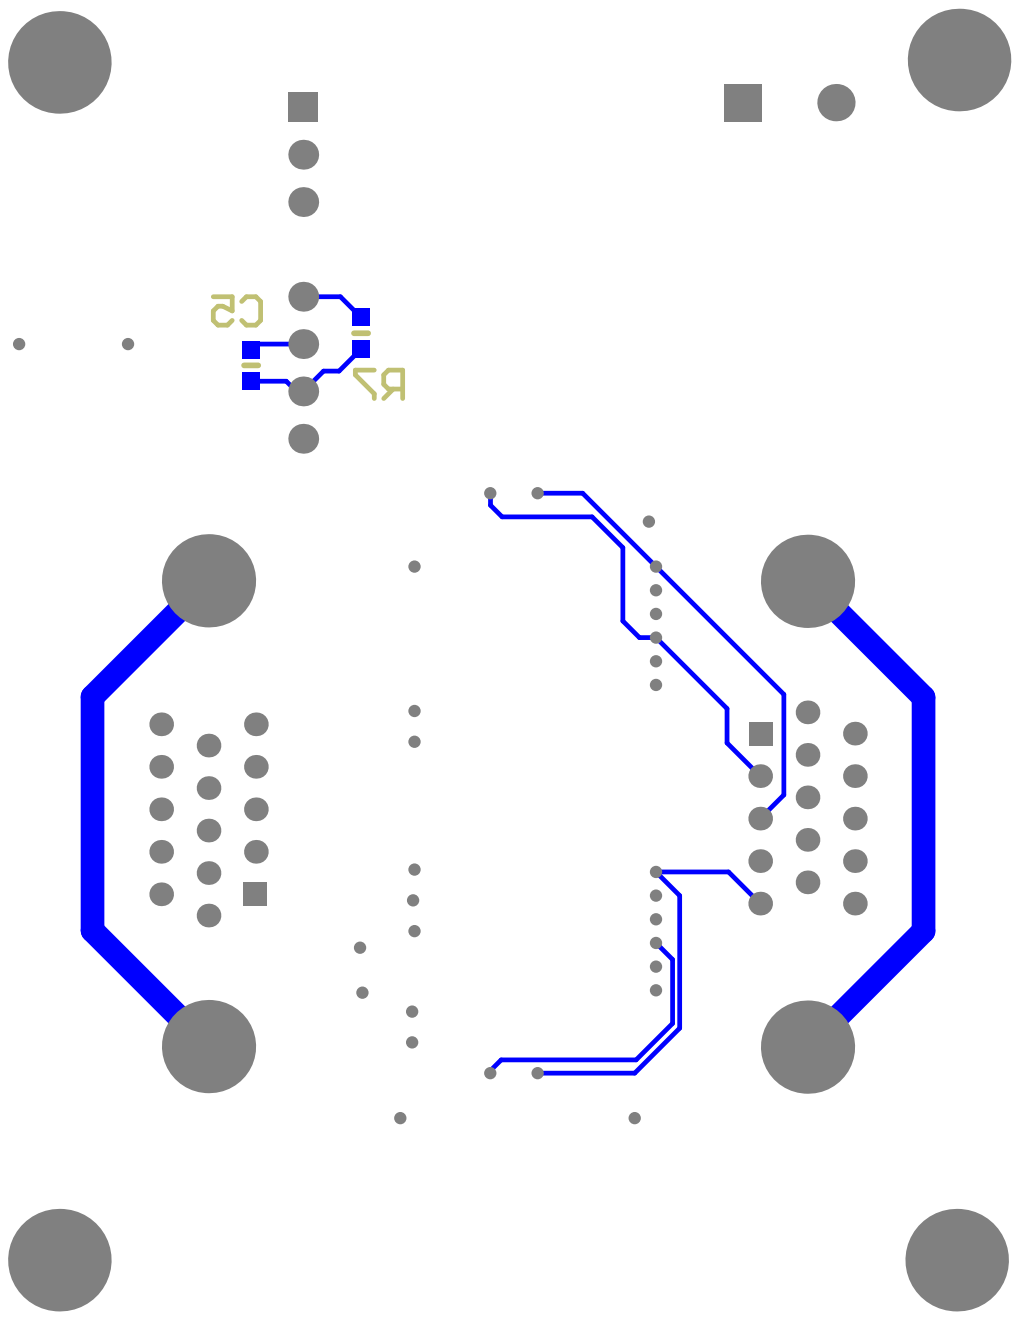
[picture p55: page 4]
