Severson-Group/AMDS/Mainboard/Firmware/mainboard/Core/Src/drv_spi.c

#include "drv_spi.h"
#include "defines.h"
#include "platform.h"
#include <stdint.h>

static void MX_SPI2_Init(void);
static void MX_SPI3_Init(void);

static SPI_HandleTypeDef hspi1;
static SPI_HandleTypeDef hspi2;
static SPI_HandleTypeDef hspi3;
static SPI_HandleTypeDef hspi4;
static SPI_HandleTypeDef hspi5;
static SPI_HandleTypeDef hspi6;

static void MX_SPI_ADC_Init(SPI_HandleTypeDef *handle, SPI_TypeDef *instance);

void drv_spi_init(void)
{
    //    MX_SPI2_Init();
    //    MX_SPI3_Init();

    MX_SPI_ADC_Init(&hspi1, SPI1);
    MX_SPI_ADC_Init(&hspi4, SPI4);
    MX_SPI_ADC_Init(&hspi5, SPI5);
    MX_SPI_ADC_Init(&hspi6, SPI6);

    // Start SPIs to daughter cards
    //
    // This causes the SPI peripherals to actively
    // drive the clock lines to the right polarity.
    __HAL_SPI_ENABLE(&hspi1);
    __HAL_SPI_ENABLE(&hspi4);
    __HAL_SPI_ENABLE(&hspi5);
    __HAL_SPI_ENABLE(&hspi6);
}

static void MX_SPI_ADC_Init(SPI_HandleTypeDef *handle, SPI_TypeDef *instance)
{
    handle->Instance = instance;
    handle->Init.Mode = SPI_MODE_MASTER;

    // Weird things happen if you don't use 2 lines mode...
    handle->Init.Direction = SPI_DIRECTION_2LINES;

    handle->Init.DataSize = SPI_DATASIZE_16BIT;
    handle->Init.CLKPolarity = SPI_POLARITY_HIGH;
    handle->Init.CLKPhase = SPI_PHASE_2EDGE;
    handle->Init.NSS = SPI_NSS_SOFT;
    handle->Init.BaudRatePrescaler = SPI_BAUDRATEPRESCALER_4;
    handle->Init.FirstBit = SPI_FIRSTBIT_MSB;

    handle->Init.TIMode = SPI_TIMODE_DISABLE;
    handle->Init.CRCCalculation = SPI_CRCCALCULATION_DISABLE;
    handle->Init.CRCPolynomial = 7;
    handle->Init.CRCLength = SPI_CRC_LENGTH_DATASIZE;
    handle->Init.NSSPMode = SPI_NSS_PULSE_DISABLE;

    if (HAL_SPI_Init(handle) != HAL_OK) {
        PANIC;
    }
}

static void MX_SPI2_Init(void)
{
    hspi2.Instance = SPI2;
    hspi2.Init.Mode = SPI_MODE_MASTER;
    hspi2.Init.Direction = SPI_DIRECTION_2LINES;
    hspi2.Init.DataSize = SPI_DATASIZE_4BIT;
    hspi2.Init.CLKPolarity = SPI_POLARITY_LOW;
    hspi2.Init.CLKPhase = SPI_PHASE_1EDGE;
    hspi2.Init.NSS = SPI_NSS_HARD_OUTPUT;
    hspi2.Init.BaudRatePrescaler = SPI_BAUDRATEPRESCALER_2;
    hspi2.Init.FirstBit = SPI_FIRSTBIT_MSB;
    hspi2.Init.TIMode = SPI_TIMODE_DISABLE;
    hspi2.Init.CRCCalculation = SPI_CRCCALCULATION_DISABLE;
    hspi2.Init.CRCPolynomial = 7;
    hspi2.Init.CRCLength = SPI_CRC_LENGTH_DATASIZE;
    hspi2.Init.NSSPMode = SPI_NSS_PULSE_ENABLE;

    if (HAL_SPI_Init(&hspi2) != HAL_OK) {
        PANIC;
    }
}

static void MX_SPI3_Init(void)
{
    hspi3.Instance = SPI3;
    hspi3.Init.Mode = SPI_MODE_MASTER;
    hspi3.Init.Direction = SPI_DIRECTION_2LINES;
    hspi3.Init.DataSize = SPI_DATASIZE_4BIT;
    hspi3.Init.CLKPolarity = SPI_POLARITY_LOW;
    hspi3.Init.CLKPhase = SPI_PHASE_1EDGE;
    hspi3.Init.NSS = SPI_NSS_HARD_OUTPUT;
    hspi3.Init.BaudRatePrescaler = SPI_BAUDRATEPRESCALER_2;
    hspi3.Init.FirstBit = SPI_FIRSTBIT_MSB;
    hspi3.Init.TIMode = SPI_TIMODE_DISABLE;
    hspi3.Init.CRCCalculation = SPI_CRCCALCULATION_DISABLE;
    hspi3.Init.CRCPolynomial = 7;
    hspi3.Init.CRCLength = SPI_CRC_LENGTH_DATASIZE;
    hspi3.Init.NSSPMode = SPI_NSS_PULSE_ENABLE;

    if (HAL_SPI_Init(&hspi3) != HAL_OK) {
        PANIC;
    }
}

void HAL_SPI_MspInit(SPI_HandleTypeDef *spiHandle)
{

    GPIO_InitTypeDef GPIO_InitStruct = { 0 };

    if (spiHandle->Instance == SPI1) {
        // SPI1 clock enable
        __HAL_RCC_SPI1_CLK_ENABLE();

        __HAL_RCC_GPIOA_CLK_ENABLE();
        // SPI1 GPIO Configuration
        // PA5     ------> SPI1_SCK
        // PA6     ------> SPI1_MISO
        GPIO_InitStruct.Pin = GPIO_PIN_5 | GPIO_PIN_6;
        GPIO_InitStruct.Mode = GPIO_MODE_AF_PP;
        GPIO_InitStruct.Pull = GPIO_NOPULL;
        GPIO_InitStruct.Speed = GPIO_SPEED_FREQ_VERY_HIGH;
        GPIO_InitStruct.Alternate = GPIO_AF5_SPI1;
        HAL_GPIO_Init(GPIOA, &GPIO_InitStruct);
    }

    else if (spiHandle->Instance == SPI2) {
        // SPI2 clock enable
        __HAL_RCC_SPI2_CLK_ENABLE();

        __HAL_RCC_GPIOB_CLK_ENABLE();
        // SPI2 GPIO Configuration
        // PB12     ------> SPI2_NSS
        // PB13     ------> SPI2_SCK
        // PB14     ------> SPI2_MISO
        // PB15     ------> SPI2_MOSI
        GPIO_InitStruct.Pin = GPIO_PIN_12 | GPIO_PIN_13 | GPIO_PIN_14 | GPIO_PIN_15;
        GPIO_InitStruct.Mode = GPIO_MODE_AF_PP;
        GPIO_InitStruct.Pull = GPIO_NOPULL;
        GPIO_InitStruct.Speed = GPIO_SPEED_FREQ_VERY_HIGH;
        GPIO_InitStruct.Alternate = GPIO_AF5_SPI2;
        HAL_GPIO_Init(GPIOB, &GPIO_InitStruct);
    }

    else if (spiHandle->Instance == SPI3) {
        // SPI3 clock enable
        __HAL_RCC_SPI3_CLK_ENABLE();

        __HAL_RCC_GPIOA_CLK_ENABLE();
        __HAL_RCC_GPIOC_CLK_ENABLE();
        // SPI3 GPIO Configuration
        // PA15     ------> SPI3_NSS
        // PC10     ------> SPI3_SCK
        // PC11     ------> SPI3_MISO
        // PC12     ------> SPI3_MOSI
        GPIO_InitStruct.Pin = GPIO_PIN_15;
        GPIO_InitStruct.Mode = GPIO_MODE_AF_PP;
        GPIO_InitStruct.Pull = GPIO_NOPULL;
        GPIO_InitStruct.Speed = GPIO_SPEED_FREQ_VERY_HIGH;
        GPIO_InitStruct.Alternate = GPIO_AF6_SPI3;
        HAL_GPIO_Init(GPIOA, &GPIO_InitStruct);

        GPIO_InitStruct.Pin = GPIO_PIN_10 | GPIO_PIN_11 | GPIO_PIN_12;
        GPIO_InitStruct.Mode = GPIO_MODE_AF_PP;
        GPIO_InitStruct.Pull = GPIO_NOPULL;
        GPIO_InitStruct.Speed = GPIO_SPEED_FREQ_VERY_HIGH;
        GPIO_InitStruct.Alternate = GPIO_AF6_SPI3;
        HAL_GPIO_Init(GPIOC, &GPIO_InitStruct);
    }

    else if (spiHandle->Instance == SPI4) {
        // SPI4 clock enable
        __HAL_RCC_SPI4_CLK_ENABLE();

        __HAL_RCC_GPIOE_CLK_ENABLE();
        // SPI4 GPIO Configuration
        // PE12     ------> SPI4_SCK
        // PE13     ------> SPI4_MISO
        GPIO_InitStruct.Pin = GPIO_PIN_12 | GPIO_PIN_13;
        GPIO_InitStruct.Mode = GPIO_MODE_AF_PP;
        GPIO_InitStruct.Pull = GPIO_NOPULL;
        GPIO_InitStruct.Speed = GPIO_SPEED_FREQ_VERY_HIGH;
        GPIO_InitStruct.Alternate = GPIO_AF5_SPI4;
        HAL_GPIO_Init(GPIOE, &GPIO_InitStruct);
    }

    else if (spiHandle->Instance == SPI5) {
        // SPI5 clock enable */
        __HAL_RCC_SPI5_CLK_ENABLE();

        __HAL_RCC_GPIOF_CLK_ENABLE();
        // SPI5 GPIO Configuration
        // PF7     ------> SPI5_SCK
        // PF8     ------> SPI5_MISO
        GPIO_InitStruct.Pin = GPIO_PIN_7 | GPIO_PIN_8;
        GPIO_InitStruct.Mode = GPIO_MODE_AF_PP;
        GPIO_InitStruct.Pull = GPIO_NOPULL;
        GPIO_InitStruct.Speed = GPIO_SPEED_FREQ_VERY_HIGH;
        GPIO_InitStruct.Alternate = GPIO_AF5_SPI5;
        HAL_GPIO_Init(GPIOF, &GPIO_InitStruct);
    }

    else if (spiHandle->Instance == SPI6) {
        // SPI6 clock enable
        __HAL_RCC_SPI6_CLK_ENABLE();

        __HAL_RCC_GPIOG_CLK_ENABLE();
        // SPI6 GPIO Configuration
        // PG12     ------> SPI6_MISO
        // PG13     ------> SPI6_SCK
        GPIO_InitStruct.Pin = GPIO_PIN_12 | GPIO_PIN_13;
        GPIO_InitStruct.Mode = GPIO_MODE_AF_PP;
        GPIO_InitStruct.Pull = GPIO_NOPULL;
        GPIO_InitStruct.Speed = GPIO_SPEED_FREQ_VERY_HIGH;
        GPIO_InitStruct.Alternate = GPIO_AF5_SPI6;
        HAL_GPIO_Init(GPIOG, &GPIO_InitStruct);
    }
}

void HAL_SPI_MspDeInit(SPI_HandleTypeDef *spiHandle)
{

    if (spiHandle->Instance == SPI1) {
        /* Peripheral clock disable */
        __HAL_RCC_SPI1_CLK_DISABLE();

        /**SPI1 GPIO Configuration
        PA5     ------> SPI1_SCK
        PA6     ------> SPI1_MISO
        */
        HAL_GPIO_DeInit(GPIOA, GPIO_PIN_5 | GPIO_PIN_6);
    }

    else if (spiHandle->Instance == SPI2) {
        /* Peripheral clock disable */
        __HAL_RCC_SPI2_CLK_DISABLE();

        /**SPI2 GPIO Configuration
        PB12     ------> SPI2_NSS
        PB13     ------> SPI2_SCK
        PB14     ------> SPI2_MISO
        PB15     ------> SPI2_MOSI
        */
        HAL_GPIO_DeInit(GPIOB, GPIO_PIN_12 | GPIO_PIN_13 | GPIO_PIN_14 | GPIO_PIN_15);
    }

    else if (spiHandle->Instance == SPI3) {
        /* Peripheral clock disable */
        __HAL_RCC_SPI3_CLK_DISABLE();

        /**SPI3 GPIO Configuration
        PA15     ------> SPI3_NSS
        PC10     ------> SPI3_SCK
        PC11     ------> SPI3_MISO
        PC12     ------> SPI3_MOSI
        */
        HAL_GPIO_DeInit(GPIOA, GPIO_PIN_15);

        HAL_GPIO_DeInit(GPIOC, GPIO_PIN_10 | GPIO_PIN_11 | GPIO_PIN_12);

    }

    else if (spiHandle->Instance == SPI4) {
        /* Peripheral clock disable */
        __HAL_RCC_SPI4_CLK_DISABLE();

        /**SPI4 GPIO Configuration
        PE12     ------> SPI4_SCK
        PE13     ------> SPI4_MISO
        */
        HAL_GPIO_DeInit(GPIOE, GPIO_PIN_12 | GPIO_PIN_13);
    }

    else if (spiHandle->Instance == SPI5) {
        /* Peripheral clock disable */
        __HAL_RCC_SPI5_CLK_DISABLE();

        /**SPI5 GPIO Configuration
        PF7     ------> SPI5_SCK
        PF8     ------> SPI5_MISO
        */
        HAL_GPIO_DeInit(GPIOF, GPIO_PIN_7 | GPIO_PIN_8);
    } else if (spiHandle->Instance == SPI6) {
        /* Peripheral clock disable */
        __HAL_RCC_SPI6_CLK_DISABLE();

        /**SPI6 GPIO Configuration
        PG12     ------> SPI6_MISO
        PG13     ------> SPI6_SCK
        */
        HAL_GPIO_DeInit(GPIOG, GPIO_PIN_12 | GPIO_PIN_13);
    }
}
