Severson-Group/AMDS/Mainboard/Firmware/mainboard/Core/Src/drv_gpio.c

#include "drv_gpio.h"
#include "defines.h"
#include "platform.h"

static void MX_GPIO_Init(void);

void drv_gpio_init(void)
{
    MX_GPIO_Init();
}

static void MX_GPIO_Init(void)
{
    GPIO_InitTypeDef GPIO_InitStruct = { 0 };

    // GPIO Ports Clock Enable
    __HAL_RCC_GPIOF_CLK_ENABLE();
    __HAL_RCC_GPIOH_CLK_ENABLE();
    __HAL_RCC_GPIOA_CLK_ENABLE();
    __HAL_RCC_GPIOE_CLK_ENABLE();
    __HAL_RCC_GPIOB_CLK_ENABLE();
    __HAL_RCC_GPIOD_CLK_ENABLE();
    __HAL_RCC_GPIOG_CLK_ENABLE();
    __HAL_RCC_GPIOC_CLK_ENABLE();

    // Configure GPIO pin Output Level
    HAL_GPIO_WritePin(GPIOF, GPIO_PIN_6, GPIO_PIN_RESET);

    // Configure GPIO pin Output Level
    HAL_GPIO_WritePin(GPIOA, GPIO_PIN_4, GPIO_PIN_RESET);

    // Configure GPIO pin Output Level
    HAL_GPIO_WritePin(GPIOE, GPIO_PIN_10 | GPIO_PIN_11, GPIO_PIN_RESET);

    // Configure GPIO pin Output Level
    HAL_GPIO_WritePin(GPIOD,
                      GPIO_PIN_8 | GPIO_PIN_9 | GPIO_PIN_10 | GPIO_PIN_11 | GPIO_PIN_3 | GPIO_PIN_4 | GPIO_PIN_5
                          | GPIO_PIN_6 | GPIO_PIN_7,
                      GPIO_PIN_RESET);

    // Configure GPIO pin Output Level
    HAL_GPIO_WritePin(GPIOG, GPIO_PIN_8 | GPIO_PIN_10, GPIO_PIN_RESET);

    // Configure GPIO pin Output Level
    HAL_GPIO_WritePin(GPIOB, GPIO_PIN_5 | GPIO_PIN_6 | GPIO_PIN_7 | GPIO_PIN_8, GPIO_PIN_RESET);

    // Configure GPIO pin : PF6
    GPIO_InitStruct.Pin = GPIO_PIN_6;
    GPIO_InitStruct.Mode = GPIO_MODE_OUTPUT_PP;
    GPIO_InitStruct.Pull = GPIO_NOPULL;
    GPIO_InitStruct.Speed = GPIO_SPEED_FREQ_LOW;
    HAL_GPIO_Init(GPIOF, &GPIO_InitStruct);

    // Configure GPIO pin : PF9
    GPIO_InitStruct.Pin = GPIO_PIN_9;
    GPIO_InitStruct.Mode = GPIO_MODE_IT_RISING;
    GPIO_InitStruct.Pull = GPIO_NOPULL;
    HAL_GPIO_Init(GPIOF, &GPIO_InitStruct);

    // Configure GPIO pin : PA4
    GPIO_InitStruct.Pin = GPIO_PIN_4;
    GPIO_InitStruct.Mode = GPIO_MODE_OUTPUT_PP;
    GPIO_InitStruct.Pull = GPIO_NOPULL;
    GPIO_InitStruct.Speed = GPIO_SPEED_FREQ_LOW;
    HAL_GPIO_Init(GPIOA, &GPIO_InitStruct);

    // Configure GPIO pin : PA7
    GPIO_InitStruct.Pin = GPIO_PIN_7;
    GPIO_InitStruct.Mode = GPIO_MODE_IT_RISING;
    GPIO_InitStruct.Pull = GPIO_NOPULL;
    HAL_GPIO_Init(GPIOA, &GPIO_InitStruct);

    // Configure GPIO pins : PE10 PE11
    GPIO_InitStruct.Pin = GPIO_PIN_10 | GPIO_PIN_11;
    GPIO_InitStruct.Mode = GPIO_MODE_OUTPUT_PP;
    GPIO_InitStruct.Pull = GPIO_NOPULL;
    GPIO_InitStruct.Speed = GPIO_SPEED_FREQ_LOW;
    HAL_GPIO_Init(GPIOE, &GPIO_InitStruct);

    // Configure GPIO pins : PD8 PD9 PD10 PD11
    //                                     PD3
    //                         PD4 PD5 PD6 PD7
    GPIO_InitStruct.Pin = GPIO_PIN_8 | GPIO_PIN_9 | GPIO_PIN_10 | GPIO_PIN_11 | GPIO_PIN_3 | GPIO_PIN_4 | GPIO_PIN_5
        | GPIO_PIN_6 | GPIO_PIN_7;
    GPIO_InitStruct.Mode = GPIO_MODE_OUTPUT_PP;
    GPIO_InitStruct.Pull = GPIO_NOPULL;
    GPIO_InitStruct.Speed = GPIO_SPEED_FREQ_LOW;
    HAL_GPIO_Init(GPIOD, &GPIO_InitStruct);

    // Configure GPIO pins : PG8 PG10
    GPIO_InitStruct.Pin = GPIO_PIN_8 | GPIO_PIN_10;
    GPIO_InitStruct.Mode = GPIO_MODE_OUTPUT_PP;
    GPIO_InitStruct.Pull = GPIO_NOPULL;
    GPIO_InitStruct.Speed = GPIO_SPEED_FREQ_LOW;
    HAL_GPIO_Init(GPIOG, &GPIO_InitStruct);

    // Configure GPIO pin : PG11
    GPIO_InitStruct.Pin = GPIO_PIN_11;
    GPIO_InitStruct.Mode = GPIO_MODE_AF_PP;
    GPIO_InitStruct.Pull = GPIO_NOPULL;
    GPIO_InitStruct.Speed = GPIO_SPEED_FREQ_LOW;
    GPIO_InitStruct.Alternate = GPIO_AF15_EVENTOUT;
    HAL_GPIO_Init(GPIOG, &GPIO_InitStruct);

    // Configure GPIO pin : PG15
    GPIO_InitStruct.Pin = GPIO_PIN_15;
    GPIO_InitStruct.Mode = GPIO_MODE_IT_RISING;
    GPIO_InitStruct.Pull = GPIO_NOPULL;
    HAL_GPIO_Init(GPIOG, &GPIO_InitStruct);

    // Configure GPIO pins : PB5 PB6 PB7 PB8
    GPIO_InitStruct.Pin = GPIO_PIN_5 | GPIO_PIN_6 | GPIO_PIN_7 | GPIO_PIN_8;
    GPIO_InitStruct.Mode = GPIO_MODE_OUTPUT_PP;
    GPIO_InitStruct.Pull = GPIO_NOPULL;
    GPIO_InitStruct.Speed = GPIO_SPEED_FREQ_LOW;
    HAL_GPIO_Init(GPIOB, &GPIO_InitStruct);
}
