Severson-Group/AMDS/Mainboard/Firmware/mainboard/Core/Src/drv_clock.c

#include "drv_clock.h"
#include "defines.h"
#include "platform.h"

void drv_clock_init(void)
{
    RCC_OscInitTypeDef RCC_OscInitStruct = { 0 };
    RCC_ClkInitTypeDef RCC_ClkInitStruct = { 0 };
    RCC_PeriphCLKInitTypeDef PeriphClkInitStruct = { 0 };

    // Configure the main internal regulator output voltage
    __HAL_RCC_PWR_CLK_ENABLE();
    __HAL_PWR_VOLTAGESCALING_CONFIG(PWR_REGULATOR_VOLTAGE_SCALE1);

    // Initializes the CPU, AHB and APB busses clocks
    RCC_OscInitStruct.OscillatorType = RCC_OSCILLATORTYPE_HSE;
    RCC_OscInitStruct.HSEState = RCC_HSE_ON;
    RCC_OscInitStruct.PLL.PLLState = RCC_PLL_ON;
    RCC_OscInitStruct.PLL.PLLSource = RCC_PLLSOURCE_HSE;
    RCC_OscInitStruct.PLL.PLLM = 4;
    RCC_OscInitStruct.PLL.PLLN = 200;
    RCC_OscInitStruct.PLL.PLLP = RCC_PLLP_DIV2;
    RCC_OscInitStruct.PLL.PLLQ = 2;

    if (HAL_RCC_OscConfig(&RCC_OscInitStruct) != HAL_OK) {
        PANIC;
    }

    // Activate the Over-Drive mode
    if (HAL_PWREx_EnableOverDrive() != HAL_OK) {
        PANIC;
    }

    // Initializes the CPU, AHB and APB busses clocks
    RCC_ClkInitStruct.ClockType = RCC_CLOCKTYPE_HCLK | RCC_CLOCKTYPE_SYSCLK | RCC_CLOCKTYPE_PCLK1 | RCC_CLOCKTYPE_PCLK2;
    RCC_ClkInitStruct.SYSCLKSource = RCC_SYSCLKSOURCE_PLLCLK;
    RCC_ClkInitStruct.AHBCLKDivider = RCC_SYSCLK_DIV1;
    RCC_ClkInitStruct.APB1CLKDivider = RCC_HCLK_DIV4;
    RCC_ClkInitStruct.APB2CLKDivider = RCC_HCLK_DIV2;

    if (HAL_RCC_ClockConfig(&RCC_ClkInitStruct, FLASH_LATENCY_6) != HAL_OK) {
        PANIC;
    }

    PeriphClkInitStruct.PeriphClockSelection = RCC_PERIPHCLK_USART2 | RCC_PERIPHCLK_USART3 | RCC_PERIPHCLK_I2C2;
    PeriphClkInitStruct.Usart2ClockSelection = RCC_USART2CLKSOURCE_PCLK1;
    PeriphClkInitStruct.Usart3ClockSelection = RCC_USART3CLKSOURCE_PCLK1;
    PeriphClkInitStruct.I2c2ClockSelection = RCC_I2C2CLKSOURCE_PCLK1;

    if (HAL_RCCEx_PeriphCLKConfig(&PeriphClkInitStruct) != HAL_OK) {
        PANIC;
    }
}
